pulp-platform/ara/docs/source/images/shuffling_logic_vary_sew.png

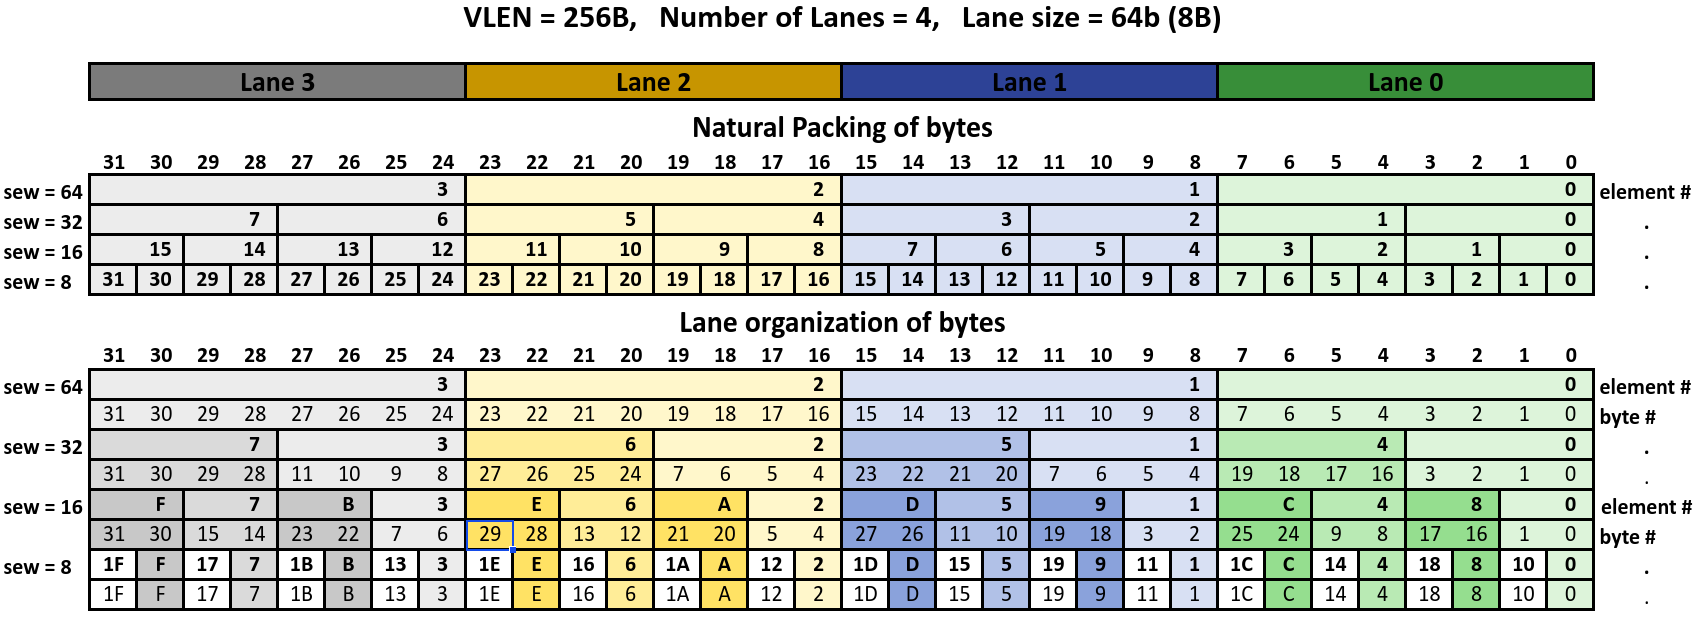
docs/source/images/shuffling_logic_vary_sew.png
