pulp-platform/ara/apps/fdotproduct/main.c

// Copyright 2022 ETH Zurich and University of Bologna.
//
// SPDX-License-Identifier: Apache-2.0
//
// Licensed under the Apache License, Version 2.0 (the "License");
// you may not use this file except in compliance with the License.
// You may obtain a copy of the License at
//
//    http://www.apache.org/licenses/LICENSE-2.0
//
// Unless required by applicable law or agreed to in writing, software
// distributed under the License is distributed on an "AS IS" BASIS,
// WITHOUT WARRANTIES OR CONDITIONS OF ANY KIND, either express or implied.
// See the License for the specific language governing permissions and
// limitations under the License.

// Author: Matteo Perotti <mperotti@iis.ee.ethz.ch>

#include <stdint.h>
#include <string.h>

#include "runtime.h"
#include "util.h"

#include "kernel/fdotproduct.h"

#ifdef SPIKE
#include <stdio.h>
#elif defined ARA_LINUX
#include <stdio.h>
#else
#include "printf.h"
#endif

// Threshold for FP comparisons
#define THRESHOLD_64b 0.0000000001
#define THRESHOLD_32b 0.0001
#define THRESHOLD_16b 1

// Run also the scalar benchmark
#define SCALAR 1

// Check the vector results against golden vectors
#define CHECK 1

// Macro to check similarity between two fp-values, wrt a threshold
#define fp_check(a, b, threshold) ((((a - b) < 0) ? b - a : a - b) < threshold)

// Vector size (Byte)
extern uint64_t vsize;
// Input vectors
extern double v64a[] __attribute__((aligned(32 * NR_LANES), section(".l2")));
extern double v64b[] __attribute__((aligned(32 * NR_LANES), section(".l2")));
extern float v32a[] __attribute__((aligned(32 * NR_LANES), section(".l2")));
extern float v32b[] __attribute__((aligned(32 * NR_LANES), section(".l2")));
extern _Float16 v16a[] __attribute__((aligned(32 * NR_LANES), section(".l2")));
extern _Float16 v16b[] __attribute__((aligned(32 * NR_LANES), section(".l2")));
// Golden outputs
extern double gold64;
extern float gold32;
extern _Float16 gold16;
// Output vectors
extern double res64_v, res64_s;
extern float res32_v, res32_s;
extern _Float16 res16_v, res16_s;

int main() {
  printf("\n");
  printf("===========\n");
  printf("=  FDOTP  =\n");
  printf("===========\n");
  printf("\n");
  printf("\n");

  uint64_t runtime_s, runtime_v;

  for (uint64_t avl = 8; avl <= (vsize >> 3); avl *= 8) {
    printf("Calulating 64b dotp with vectors with length = %lu\n", avl);
    start_timer();
    res64_v = fdotp_v64b(v64a, v64b, avl);
    stop_timer();
    runtime_v = get_timer();
    printf("Vector runtime: %ld\n", runtime_v);

    if (SCALAR) {
      start_timer();
      res64_s = fdotp_s64b(v64a, v64b, avl);
      stop_timer();
      runtime_s = get_timer();
      printf("Scalar runtime: %ld\n", runtime_s);
    }

    if (CHECK) {
      if (SCALAR) {
        printf("Checking results: v = %f, s = %f\n", res64_v, res64_s);
        if (!similarity_check(res64_v, res64_s, THRESHOLD_64b)) {
          printf("Error: v = %f, s = %f\n", res64_v, res64_s);
          return -1;
        }
      }
    }
  }

  for (uint64_t avl = 8; avl <= (vsize >> 2); avl *= 8) {
    printf("Calulating 32b dotp with vectors with length = %lu\n", avl);
    start_timer();
    res32_v = fdotp_v32b(v32a, v32b, avl);
    stop_timer();
    runtime_v = get_timer();
    printf("Vector runtime: %ld\n", runtime_v);

    if (SCALAR) {
      start_timer();
      res32_s = fdotp_s32b(v32a, v32b, avl);
      stop_timer();
      runtime_s = get_timer();
      printf("Scalar runtime: %ld\n", runtime_s);
    }

    if (CHECK) {
      if (SCALAR) {
        printf("Checking results: v = %f, s = %f\n", res32_v, res32_s);
        if (!similarity_check(res32_v, res32_s, THRESHOLD_32b)) {
          printf("Error: v = %f, s = %f\n", res32_v, res32_s);
          return -1;
        }
      }
    }
  }

  for (uint64_t avl = 8; avl <= (vsize >> 2); avl *= 8) {
    // Dotp
    printf("Calulating 16b dotp with vectors with length = %lu\n", avl);
    start_timer();
    res16_v = fdotp_v16b(v16a, v16b, avl);
    stop_timer();
    runtime_v = get_timer();
    printf("Vector runtime: %ld\n", runtime_v);

    if (SCALAR) {
      start_timer();
      res16_s = fdotp_s16b(v16a, v16b, avl);
      stop_timer();
      runtime_s = get_timer();
      printf("Scalar runtime: %ld\n", runtime_s);
    }

    if (CHECK) {
      if (SCALAR) {
        printf("Checking results: v = %x, s = %x\n", *((uint16_t *)&res16_v),
               *((uint16_t *)&res16_s));
        if (!similarity_check(res16_v, res16_s, THRESHOLD_16b)) {
          printf("Error: v = %x, s = %x\n", *((uint16_t *)&res16_v),
                 *((uint16_t *)&res16_s));
          return -1;
        }
      }
    }
  }

  printf("SUCCESS.\n");

  return 0;
}
