pulp-platform/ara/hardware/src/sldu/sldu.sv

// Copyright 2021 ETH Zurich and University of Bologna.
// Solderpad Hardware License, Version 0.51, see LICENSE for details.
// SPDX-License-Identifier: SHL-0.51
//
// Author: Matheus Cavalcante <matheusd@iis.ee.ethz.ch>
// Description:
// This is Ara's slide unit. It is responsible for running the vector slide (up/down)
// instructions, which need access to the whole Vector Register File.

module sldu import ara_pkg::*; import rvv_pkg::*; #(
    parameter  int  unsigned NrLanes        = 0,
    parameter  int  unsigned VLEN           = 0,
    parameter  crypto_support_e CryptoSupport = CryptoSupportNone,
    parameter  type          vaddr_t        = logic, // Type used to address vector register file elements,
    parameter  type          pe_req_t       = logic,
    parameter  type          pe_resp_t      = logic,
    // Dependant parameters. DO NOT CHANGE!
    localparam int  unsigned DataWidth = $bits(elen_t), // Width of the lane datapath
    localparam int  unsigned StrbWidth = DataWidth/8,
    localparam type          strb_t    = logic [StrbWidth-1:0], // Byte-strobe type
    localparam type          vlen_t    = logic[$clog2(VLEN+1)-1:0]
  ) (
    input  logic                   clk_i,
    input  logic                   rst_ni,
    // Interface with the main sequencer
    input  pe_req_t                pe_req_i,
    input  logic                   pe_req_valid_i,
    input  logic     [NrVInsn-1:0] pe_vinsn_running_i,
    output logic                   pe_req_ready_o,
    output pe_resp_t               pe_resp_o,
    // Interface with the lanes
    input  elen_t    [NrLanes-1:0] sldu_operand_i,
    input  logic     [NrLanes-1:0] sldu_operand_valid_i,
    output logic     [NrLanes-1:0] sldu_operand_ready_o,
    output logic     [NrLanes-1:0] sldu_result_req_o,
    output vid_t     [NrLanes-1:0] sldu_result_id_o,
    output vaddr_t   [NrLanes-1:0] sldu_result_addr_o,
    output elen_t    [NrLanes-1:0] sldu_result_wdata_o,
    output strb_t    [NrLanes-1:0] sldu_result_be_o,
    input  logic     [NrLanes-1:0] sldu_result_gnt_i,
    input  logic     [NrLanes-1:0] sldu_result_final_gnt_i,
    // Support for reductions
    output sldu_mux_e              sldu_mux_sel_o,
    output logic     [NrLanes-1:0] sldu_red_valid_o,
    // Interface with the Mask Unit
    input  strb_t    [NrLanes-1:0] mask_i,
    input  logic     [NrLanes-1:0] mask_valid_i,
    output logic                   mask_ready_o
  );

  `include "common_cells/registers.svh"

  import cf_math_pkg::idx_width;

  localparam int unsigned AesColsPerLane  = DataWidth / 32;
  localparam int unsigned AesColsPerGroup = 4;

  ////////////////////////////////
  //  Vector instruction queue  //
  ////////////////////////////////

  // We store a certain number of in-flight vector instructions
  localparam VInsnQueueDepth = SlduInsnQueueDepth;

  struct packed {
    pe_req_t [VInsnQueueDepth-1:0] vinsn;

    // Each instruction can be in one of the three execution phases.
    // - Being accepted (i.e., it is being stored for future execution in this
    //   vector functional unit).
    // - Being issued (i.e., its micro-operations are currently being issued
    //   to the corresponding functional units).
    // - Being committed (i.e., its results are being written to the vector
    //   register file).
    // We need pointers to index which instruction is at each execution phase
    // between the VInsnQueueDepth instructions in memory.
    logic [idx_width(VInsnQueueDepth)-1:0] accept_pnt;
    logic [idx_width(VInsnQueueDepth)-1:0] issue_pnt;
    logic [idx_width(VInsnQueueDepth)-1:0] commit_pnt;

    // We also need to count how many instructions are queueing to be
    // issued/committed, to avoid accepting more instructions than
    // we can handle.
    logic [idx_width(VInsnQueueDepth):0] issue_cnt;
    logic [idx_width(VInsnQueueDepth):0] commit_cnt;
  } vinsn_queue_d, vinsn_queue_q;

  pe_req_t vinsn_issue_q;
  logic vinsn_issue_valid_q;
  // Is the vector instruction queue full?
  logic vinsn_queue_full;
  assign vinsn_queue_full = (vinsn_queue_q.commit_cnt == VInsnQueueDepth);

  // Do we have a vector instruction ready to be issued?
  `FF(vinsn_issue_q, vinsn_queue_d.vinsn[vinsn_queue_d.issue_pnt], '0)
  `FF(vinsn_issue_valid_q, vinsn_queue_d.issue_cnt != '0, 1'b0)

  // Do we have a vector instruction with results being committed?
  pe_req_t vinsn_commit;
  logic    vinsn_commit_valid;
  assign vinsn_commit       = vinsn_queue_q.vinsn[vinsn_queue_q.commit_pnt];
  assign vinsn_commit_valid = (vinsn_queue_q.commit_cnt != '0);

  always_ff @(posedge clk_i or negedge rst_ni) begin
    if (!rst_ni) begin
      vinsn_queue_q <= '0;
    end else begin
      vinsn_queue_q <= vinsn_queue_d;
    end
  end

  /////////////////////
  //  Result queues  //
  /////////////////////

  localparam int unsigned ResultQueueDepth = 2;

  // There is a result queue per lane, holding the results that were not
  // yet accepted by the corresponding lane.
  typedef struct packed {
    vid_t id;
    vaddr_t addr;
    elen_t wdata;
    strb_t be;
  } payload_t;

  // Result queue
  payload_t [ResultQueueDepth-1:0][NrLanes-1:0] result_queue_d, result_queue_q;
  logic     [ResultQueueDepth-1:0][NrLanes-1:0] result_queue_valid_d, result_queue_valid_q;
  // We need two pointers in the result queue. One pointer to
  // indicate with `payload_t` we are currently writing into (write_pnt),
  // and one pointer to indicate which `payload_t` we are currently
  // reading from and writing into the lanes (read_pnt).
  logic     [idx_width(ResultQueueDepth)-1:0]   result_queue_write_pnt_d, result_queue_write_pnt_q;
  logic     [idx_width(ResultQueueDepth)-1:0]   result_queue_read_pnt_d, result_queue_read_pnt_q;
  // We need to count how many valid elements are there in this result queue.
  logic     [idx_width(ResultQueueDepth):0]     result_queue_cnt_d, result_queue_cnt_q;
  // Vector to register the final grants from the operand requesters, which indicate
  // that the result was actually written in the VRF (while the normal grant just says
  // that the result was accepted by the operand requester stage
  logic     [NrLanes-1:0]                       result_final_gnt_d, result_final_gnt_q;

  // Is the result queue full?
  logic result_queue_full;
  assign result_queue_full = (result_queue_cnt_q == ResultQueueDepth);
  // Is the result queue empty?
  logic result_queue_empty;
  assign result_queue_empty = (result_queue_cnt_q == '0);

  always_ff @(posedge clk_i or negedge rst_ni) begin: p_result_queue_ff
    if (!rst_ni) begin
      result_queue_q           <= '0;
      result_queue_valid_q     <= '0;
      result_queue_write_pnt_q <= '0;
      result_queue_read_pnt_q  <= '0;
      result_queue_cnt_q       <= '0;
    end else begin
      result_queue_q           <= result_queue_d;
      result_queue_valid_q     <= result_queue_valid_d;
      result_queue_write_pnt_q <= result_queue_write_pnt_d;
      result_queue_read_pnt_q  <= result_queue_read_pnt_d;
      result_queue_cnt_q       <= result_queue_cnt_d;
    end
  end

  ////////////////////////////////
  //  Spill-reg from the lanes  //
  ////////////////////////////////

  elen_t [NrLanes-1:0] sldu_operand;
  logic  [NrLanes-1:0] sldu_operand_valid;
  logic  [NrLanes-1:0] sldu_operand_ready;

  // Don't handshake if the operands target the addrgen!
  // Moreover, when computing NP2 slides, loop over the same data!
  elen_t [NrLanes-1:0] sldu_operand_d;
  logic [NrLanes-1:0]  sldu_operand_valid_d;
  logic [NrLanes-1:0]  sldu_operand_ready_q;

  typedef enum logic {
    NP2_BUFFER_PNT,
    NP2_RESULT_PNT
  } np2_result_queue_pnt_e;

  typedef enum logic {
    NP2_EXT_SEL,
    NP2_LOOP_SEL
  } np2_loop_mux_e;
  np2_loop_mux_e np2_loop_mux_sel_d, np2_loop_mux_sel_q;

  logic slide_np2_buf_valid_d, slide_np2_buf_valid_q;

  // There are multiple transmitters (TX) (OpQueue, ALU, FPU, SLDU-NP2) and receivers (RX) (SLDU, ADDRGEN).
  // Hypotheses:
  // - When valid is asserted on the RX, data cannot change anymore until the handshake happens.
  // - When valid is received by RX, then DATA is targeting that RX only.
  // Data and handshakes signals are controlled upstream (TX side) so that this Hypotheses hold.

  for (genvar l = 0; l < NrLanes; l++) begin
    spill_register #(
      .T(elen_t)
    ) i_sldu_spill_register (
      .clk_i  (clk_i                      ),
      .rst_ni (rst_ni                     ),
      .valid_i(sldu_operand_valid_d[l]    ),
      .ready_o(sldu_operand_ready_q[l]    ),
      .data_i (sldu_operand_d[l]          ),
      .valid_o(sldu_operand_valid[l]      ),
      .ready_i(sldu_operand_ready[l]      ),
      .data_o (sldu_operand[l]            )
    );

    assign sldu_operand_d[l] = np2_loop_mux_sel_q == NP2_EXT_SEL
                             ? sldu_operand_i[l]
                             : result_queue_q[NP2_BUFFER_PNT][l].wdata;

    assign sldu_operand_valid_d[l] = np2_loop_mux_sel_q == NP2_EXT_SEL
                                   ? sldu_operand_valid_i[l]
                                   : slide_np2_buf_valid_q;

    assign sldu_operand_ready_o[l] = np2_loop_mux_sel_q == NP2_EXT_SEL
                                   ? sldu_operand_ready_q[l]
                                   : 1'b0;
  end

  //////////////////////////
  //  Cut from the masku  //
  //////////////////////////

  strb_t [NrLanes-1:0] mask_q;
  logic  [NrLanes-1:0] mask_valid_d, mask_valid_q;
  logic                mask_ready_d;
  logic  [NrLanes-1:0] mask_ready_q;

  for (genvar l = 0; l < NrLanes; l++) begin
    spill_register #(
      .T(strb_t)
    ) i_mask_operand_register (
      .clk_i     (clk_i           ),
      .rst_ni    (rst_ni          ),
      .data_o    (mask_q[l]       ),
      .valid_o   (mask_valid_q[l] ),
      .ready_i   (mask_ready_d    ),
      .data_i    (mask_i[l]       ),
      .valid_i   (mask_valid_d[l] ),
      .ready_o   (mask_ready_q[l] )
    );

    // Sample only SLDU mask valid
    assign mask_valid_d[l] = mask_valid_i[l] & ~vinsn_issue_q.vm & vinsn_issue_valid_q;
  end


  // Don't upset the masku with a spurious ready
  assign mask_ready_o = mask_ready_q[0] & mask_valid_i[0] & ~vinsn_issue_q.vm & vinsn_issue_valid_q & !(vinsn_issue_q.vfu inside {VFU_Alu, VFU_MFpu});

  ///////////////////
  //  NP2 Support  //
  ///////////////////

  // The SLDU only supports powers of two (p2) strides
  // Decompose the non-power-of-two (np2) slide in multiple p2 slides

  // We implement the np2 support here and fully process every input packet
  // singularly to comply with the undisturbed policy. We cannot use the VRF
  // as intermediate buffer; each VRF write is a commit.

  typedef logic [idx_width(8*NrLanes)-1:0] stride_t;

  stride_t                                  p2_stride_gen_stride_d;
  logic                                     p2_stride_gen_valid_d;
  logic                                     p2_stride_gen_update_d;
  logic [idx_width(idx_width(8*NrLanes)):0] p2_stride_gen_popc_q;
  stride_t                                  p2_stride_gen_stride_q;
  logic                                     p2_stride_gen_valid_q;

  p2_stride_gen #(
    .NrLanes (NrLanes)
  ) i_p2_stride_gen (
    .clk_i       (clk_i                 ),
    .rst_ni      (rst_ni                ),
    .stride_i    (p2_stride_gen_stride_d),
    .valid_i     (p2_stride_gen_valid_d ),
    .update_i    (p2_stride_gen_update_d),
    .popc_o      (p2_stride_gen_popc_q  ),
    .stride_p2_o (p2_stride_gen_stride_q),
    .valid_o     (p2_stride_gen_valid_q )
  );

  //////////////////
  //  Reductions  //
  //////////////////

  // Inter-lane reductions are performed with a logarithmic tree, and the result is
  // accumulated in the last Lane. Then, in the end, the result is passed to the first
  // lane for SIMD reduction
  logic [idx_width(NrLanes)-1:0] red_stride_cnt_d, red_stride_cnt_q;
  logic [idx_width(NrLanes):0] red_stride_cnt_d_wide;

  logic is_issue_reduction, is_issue_alu_reduction, is_issue_vmfpu_reduction;

  assign is_issue_alu_reduction   = vinsn_issue_valid_q & (vinsn_issue_q.vfu == VFU_Alu)
                                  & !(Zvkned(CryptoSupport) && vinsn_issue_q.op inside {[VAESDM_VV:VAESKF2]});
  assign is_issue_vmfpu_reduction = vinsn_issue_valid_q & (vinsn_issue_q.vfu == VFU_MFpu);
  assign is_issue_reduction       = is_issue_alu_reduction | is_issue_vmfpu_reduction;

  // AES ops routed through the SLDU (ShiftRows for round ops, prefix-XOR for key schedule)
  logic is_issue_aes;
  if (Zvkned(CryptoSupport)) begin : gen_aes_issue
    assign is_issue_aes = vinsn_issue_valid_q & (vinsn_issue_q.op inside {[VAESDM_VV:VAESKF2]});
  end else begin : gen_no_aes_issue
    assign is_issue_aes = 1'b0;
  end

  // Active lane mask for AES ops: when VL < 2*NrLanes (less than one full beat),
  // only lanes 0..num_active_cols-1 participate. Column c maps to lane (c % NrLanes).
  // issue_cnt_q is in bytes; each column = 4 bytes.
  logic [NrLanes-1:0] aes_lane_mask;
  always_comb begin
    aes_lane_mask = '1;
    if (is_issue_aes) begin
      for (int unsigned l = 0; l < NrLanes; l++)
        aes_lane_mask[l] = (l < (issue_cnt_q >> 2)) || (issue_cnt_q >= (NrLanes * 8));
    end
  end

  always_comb begin
    sldu_mux_sel_o = NO_RED;
    if (((is_issue_alu_reduction || is_issue_aes) && !(vinsn_commit_valid && vinsn_commit.vfu != VFU_Alu)) || (vinsn_commit_valid && vinsn_commit.vfu == VFU_Alu)) begin
      sldu_mux_sel_o = ALU_RED;
    end else if ((is_issue_vmfpu_reduction && !(vinsn_commit_valid && vinsn_commit.vfu != VFU_MFpu)) || (vinsn_commit_valid && vinsn_commit.vfu == VFU_MFpu)) begin
      sldu_mux_sel_o = MFPU_RED;
    end
  end

  /////////////////////
  //  SLDU DataPath  //
  /////////////////////

  // Input/output non-flat operands
  elen_t [NrLanes-1:0] sld_op_src;
  elen_t [NrLanes-1:0] sld_op_dst;

  // Input and output eew for reshuffling
  rvv_pkg::vew_e sld_eew_src;
  rvv_pkg::vew_e sld_eew_dst;

  // 0: slidedown, 1: slideup
  logic sld_dir;

  // The SLDU slides by powers of two
  logic [idx_width(4*NrLanes):0] sld_slamt;

  sldu_op_dp #(
    .NrLanes  (NrLanes    )
  ) i_sldu_op_dp (
    .op_i     (sld_op_src ),
    .slamt_i  (sld_slamt  ),
    .eew_src_i(sld_eew_src),
    .eew_dst_i(sld_eew_dst),
    .dir_i    (sld_dir    ),
    .op_o     (sld_op_dst )
  );

  //////////////////
  //  Slide unit  //
  //////////////////

  // Vector instructions currently running
  logic [NrVInsn-1:0] vinsn_running_d, vinsn_running_q;

  // Interface with the main sequencer
  pe_resp_t pe_resp;

  // State of the slide FSM
  typedef enum logic [3:0] {
    SLIDE_IDLE,
    SLIDE_RUN,
    SLIDE_RUN_VSLIDE1UP_FIRST_WORD,
    SLIDE_RUN_OSUM,
    SLIDE_WAIT_OSUM,
    SLIDE_NP2_SETUP,
    SLIDE_NP2_RUN,
    SLIDE_NP2_COMMIT,
    SLIDE_NP2_WAIT
  } slide_state_e;
  slide_state_e state_d, state_q;

  logic  [8*NrLanes-1:0] out_en_flat, out_en_seq;
  strb_t [NrLanes-1:0]   out_en;

  // Pointers in the input operand and the output result
  logic   [idx_width(NrLanes*StrbWidth):0] in_pnt_d, in_pnt_q;
  logic   [idx_width(NrLanes*StrbWidth):0] out_pnt_d, out_pnt_q;
  vaddr_t                                  vrf_pnt_d, vrf_pnt_q;

  // Remaining bytes of the current instruction in the issue phase
  vlen_t issue_cnt_d, issue_cnt_q;
  // Respected by default: input_limit_d  = 8*NrLanes + out_pnt_d - in_pnt_d;
  // To enforce: output_limit_d = out_pnt_d + issue_cnt_d;
  // MAXVL == VLEN (when LMUL == 8, i.e., the maximum possible)
  logic [idx_width(VLEN+1):0] output_limit_d, output_limit_q;

  // Remaining bytes of the current instruction in the commit phase
  vlen_t commit_cnt_d, commit_cnt_q;

  /////////////////////////////////////
  //  AES Datapath (SLDU, gated)     //
  /////////////////////////////////////

  elen_t [NrLanes-1:0] aes_shift_result;
  elen_t [NrLanes-1:0] aes_kf1_result;

  if (Zvkned(CryptoSupport)) begin : gen_aes_sldu

    // ShiftRows / InvShiftRows byte permutation across AES columns.
    // With SEW=32, each AES element group is 128 bits = 4x32-bit columns.
    // Each 64-bit lane carries AesColsPerLane columns, so a beat may contain
    // multiple AES groups depending on NrLanes.
    //
    // Column layout within a 32-bit word: [7:0]=row0, [15:8]=row1, [23:16]=row2, [31:24]=row3
    //
    // ShiftRows:    row r shifts LEFT  by r across columns
    // InvShiftRows: row r shifts RIGHT by r across columns

    always_comb begin
      aes_shift_result = '0;

      for (int unsigned l = 0; l < NrLanes; l++) begin
        for (int unsigned half = 0; half < AesColsPerLane; half++) begin
          automatic int unsigned out_col_idx   = half * NrLanes + l;
          automatic int unsigned group_base    = (out_col_idx / AesColsPerGroup) * AesColsPerGroup;
          automatic int unsigned col_in_group  = out_col_idx % AesColsPerGroup;
          automatic int unsigned bit_base      = half * 32;
          automatic int unsigned row1_src_col;
          automatic int unsigned row2_src_col;
          automatic int unsigned row3_src_col;
          automatic int unsigned row1_src_lane;
          automatic int unsigned row2_src_lane;
          automatic int unsigned row3_src_lane;
          automatic int unsigned row1_src_half;
          automatic int unsigned row2_src_half;
          automatic int unsigned row3_src_half;

          if (vinsn_issue_q.op inside {VAESEM_VV, VAESEF_VV, VAESEM_VS, VAESEF_VS}) begin
            row1_src_col = group_base + ((col_in_group + 1) % AesColsPerGroup);
            row2_src_col = group_base + ((col_in_group + 2) % AesColsPerGroup);
            row3_src_col = group_base + ((col_in_group + 3) % AesColsPerGroup);
          end else begin
            row1_src_col = group_base + ((col_in_group + 3) % AesColsPerGroup);
            row2_src_col = group_base + ((col_in_group + 2) % AesColsPerGroup);
            row3_src_col = group_base + ((col_in_group + 1) % AesColsPerGroup);
          end

          row1_src_lane = row1_src_col % NrLanes;
          row2_src_lane = row2_src_col % NrLanes;
          row3_src_lane = row3_src_col % NrLanes;
          row1_src_half = row1_src_col / NrLanes;
          row2_src_half = row2_src_col / NrLanes;
          row3_src_half = row3_src_col / NrLanes;

          aes_shift_result[l][bit_base +  0 +: 8] = sldu_operand[l            ][bit_base              +  0 +: 8];
          aes_shift_result[l][bit_base +  8 +: 8] = sldu_operand[row1_src_lane][row1_src_half * 32 +  8 +: 8];
          aes_shift_result[l][bit_base + 16 +: 8] = sldu_operand[row2_src_lane][row2_src_half * 32 + 16 +: 8];
          aes_shift_result[l][bit_base + 24 +: 8] = sldu_operand[row3_src_lane][row3_src_half * 32 + 24 +: 8];
        end
      end
    end

    // Key schedule prefix-XOR chain (shared by vaeskf1 and vaeskf2).
    // Input from VALU: [w0, w1, w2, temp] where temp = SubWord(RotWord(w3)) ^ Rcon
    // Output to VALU:  [nw0, nw1, nw2, nw2] where nwi = wi ^ nw(i-1), nw(-1) = temp
    // The w3 position gets nw2 so the VALU can compute nw3 = w3 ^ nw2.

    localparam int unsigned AesGroupsPerBeat = (NrLanes * AesColsPerLane) / AesColsPerGroup;

    function automatic logic [31:0] kf1_extract(
      input elen_t [NrLanes-1:0] data,
      input int unsigned col
    );
      kf1_extract = data[col % NrLanes][(col / NrLanes) * 32 +: 32];
    endfunction

    always_comb begin
      aes_kf1_result = '0;

      for (int unsigned grp = 0; grp < AesGroupsPerBeat; grp++) begin
        automatic logic [31:0] w0   = kf1_extract(sldu_operand, grp * 4 + 0);
        automatic logic [31:0] w1   = kf1_extract(sldu_operand, grp * 4 + 1);
        automatic logic [31:0] w2   = kf1_extract(sldu_operand, grp * 4 + 2);
        automatic logic [31:0] temp = kf1_extract(sldu_operand, grp * 4 + 3);

        automatic logic [31:0] nw0 = w0 ^ temp;
        automatic logic [31:0] nw1 = w1 ^ nw0;
        automatic logic [31:0] nw2 = w2 ^ nw1;

        automatic int unsigned c0_lane = (grp * 4 + 0) % NrLanes;
        automatic int unsigned c0_half = (grp * 4 + 0) / NrLanes;
        automatic int unsigned c1_lane = (grp * 4 + 1) % NrLanes;
        automatic int unsigned c1_half = (grp * 4 + 1) / NrLanes;
        automatic int unsigned c2_lane = (grp * 4 + 2) % NrLanes;
        automatic int unsigned c2_half = (grp * 4 + 2) / NrLanes;
        automatic int unsigned c3_lane = (grp * 4 + 3) % NrLanes;
        automatic int unsigned c3_half = (grp * 4 + 3) / NrLanes;

        aes_kf1_result[c0_lane][c0_half * 32 +: 32] = nw0;
        aes_kf1_result[c1_lane][c1_half * 32 +: 32] = nw1;
        aes_kf1_result[c2_lane][c2_half * 32 +: 32] = nw2;
        aes_kf1_result[c3_lane][c3_half * 32 +: 32] = nw2; // w3 position gets nw2
      end
    end

  end else begin : gen_no_aes_sldu
    assign aes_shift_result = '0;
    assign aes_kf1_result   = '0;
  end

  always_comb begin: p_sldu
    // Maintain state
    vinsn_queue_d = vinsn_queue_q;
    issue_cnt_d   = issue_cnt_q;
    commit_cnt_d  = commit_cnt_q;
    in_pnt_d      = in_pnt_q;
    out_pnt_d     = out_pnt_q;
    vrf_pnt_d     = vrf_pnt_q;
    state_d       = state_q;

    result_queue_d           = result_queue_q;
    result_queue_valid_d     = result_queue_valid_q;
    result_queue_read_pnt_d  = result_queue_read_pnt_q;
    result_queue_write_pnt_d = result_queue_write_pnt_q;
    result_queue_cnt_d       = result_queue_cnt_q;

    result_final_gnt_d = result_final_gnt_q;

    // Vector instructions currently running
    vinsn_running_d = vinsn_running_q & pe_vinsn_running_i;

    out_en_flat    = '0;
    out_en_seq     = '0;
    out_en         = '0;
    output_limit_d = output_limit_q;

    // We are not ready, by default
    pe_resp            = '0;
    mask_ready_d       = 1'b0;
    sldu_operand_ready = '0;

    red_stride_cnt_d = red_stride_cnt_q;

    p2_stride_gen_stride_d = '0;
    p2_stride_gen_valid_d  = 1'b0;
    p2_stride_gen_update_d = 1'b0;

    np2_loop_mux_sel_d    = np2_loop_mux_sel_q;
    slide_np2_buf_valid_d = slide_np2_buf_valid_q;

    red_stride_cnt_d_wide = {red_stride_cnt_q, red_stride_cnt_q[idx_width(NrLanes)-1]};

    // Inform the main sequencer if we are idle
    pe_req_ready_o = !vinsn_queue_full;

    // Slide Unit DP
    sld_op_src  = sldu_operand;
    sld_eew_src = (vinsn_issue_q.vfu inside {VFU_Alu, VFU_MFpu})
                ? vinsn_issue_q.vtype.vsew
                : vinsn_issue_q.eew_vs2;
    sld_eew_dst = vinsn_issue_q.vtype.vsew;
    sld_dir     = (vinsn_issue_q.op == VSLIDEUP) || (vinsn_issue_q.vfu inside {VFU_Alu, VFU_MFpu});
    sld_slamt   = (vinsn_issue_q.vfu inside {VFU_Alu, VFU_MFpu})
                ? red_stride_cnt_q
                : stride_t'(vinsn_issue_q.stride >> vinsn_issue_q.vtype.vsew);

    /////////////////
    //  Slide FSM  //
    /////////////////

    unique case (state_q)
      SLIDE_IDLE: begin
        if (vinsn_issue_valid_q) begin
          state_d   = vinsn_issue_q.is_stride_np2 ? SLIDE_NP2_SETUP : SLIDE_RUN;
          vrf_pnt_d = '0;

          unique case (vinsn_issue_q.op)
            VSLIDEUP: begin
              // vslideup starts reading the source operand from its beginning
              in_pnt_d  = '0;
              // vslideup starts writing the destination vector at the slide offset
              out_pnt_d = vinsn_issue_q.stride[idx_width(8*NrLanes)-1:0];

              // Initialize counters
              issue_cnt_d = vinsn_issue_q.vl << int'(vinsn_issue_q.vtype.vsew);

              // Initialize be-enable-generation ancillary signals
              output_limit_d = vinsn_issue_q.use_scalar_op ? out_pnt_d + issue_cnt_d : issue_cnt_d;

              // Trim vector elements which are not touched by the slide unit
              issue_cnt_d -= vinsn_issue_q.stride[$bits(issue_cnt_d)-1:0];

              // Start writing at the middle of the destination vector
              vrf_pnt_d = vinsn_issue_q.stride >> $clog2(8*NrLanes);

              // Go to SLIDE_RUN_VSLIDE1UP_FIRST_WORD if this is a vslide1up instruction
              if (vinsn_issue_q.use_scalar_op)
                state_d = SLIDE_RUN_VSLIDE1UP_FIRST_WORD;
            end
            VSLIDEDOWN: begin
              // vslidedown starts reading the source operand from the slide offset
              in_pnt_d  = vinsn_issue_q.stride[idx_width(8*NrLanes)-1:0];
              // vslidedown starts writing the destination vector at its beginning
              out_pnt_d = '0;

              // Initialize counters
              issue_cnt_d = vinsn_issue_q.vl << int'(vinsn_issue_q.vtype.vsew);

              // Initialize be-enable-generation ancillary signals
              output_limit_d = vinsn_issue_q.use_scalar_op
                             ? issue_cnt_d - (1 << int'(vinsn_issue_q.vtype.vsew))
                             : issue_cnt_d;

              // Trim the last element of vslide1down, which does not come from the VRF
              if (vinsn_issue_q.use_scalar_op)
                issue_cnt_d -= 1 << int'(vinsn_issue_q.vtype.vsew);
            end
            // Ordered sum reductions
            VFREDOSUM, VFWREDOSUM: begin
              // Ordered redsum instructions doesn't need in/out_pnt
              in_pnt_d  = '0;
              out_pnt_d = '0;

              // The total number of transactions is vl - 1, but the last data is sent
              // to lane 0
              issue_cnt_d  = vinsn_issue_q.vl;

              state_d = SLIDE_RUN_OSUM;
            end
            // AES ops: ShiftRows for round ops, prefix-XOR for key schedule.
            // Each beat processes NrLanes*8 bytes; total bytes = VL * 4 (SEW=32).
            // Note: vsew was overridden to EW64 at accept time, so use EW32 explicitly.
            VAESDM_VV, VAESDF_VV, VAESEM_VV, VAESEF_VV, VAESDM_VS, VAESDF_VS, VAESEM_VS, VAESEF_VS, VAESKF1, VAESKF2:  if (Zvkned(CryptoSupport)) begin
              in_pnt_d  = '0;
              out_pnt_d = '0;
              issue_cnt_d = vinsn_issue_q.vl << unsigned'(rvv_pkg::EW32);
            end
            // Unordered reductions
            default: begin
              // Unordered redsum instructions doesn't need in/out_pnt
              in_pnt_d  = '0;
              out_pnt_d = '0;

              // Initialize issue cnt. Pretend to move NrLanes 64-bit elements for (clog2(NrLanes) + 1) times.
              issue_cnt_d  = (NrLanes * ($clog2(NrLanes) + 1)) << EW64;
            end
          endcase
        end
      end

      SLIDE_RUN, SLIDE_RUN_VSLIDE1UP_FIRST_WORD, SLIDE_NP2_COMMIT: begin
        // Are we ready?
        // During a reduction (vinsn_issue_q.vfu == VFU_Alu/VFU_MFPU) don't wait for mask bits
        if ((&(sldu_operand_valid | ~aes_lane_mask) ||
           (((vinsn_issue_q.stride[$bits(vinsn_issue_q.vl)-1:0] >> vinsn_issue_q.vtype.vsew) >= vinsn_issue_q.vl) &&
           (state_q == SLIDE_RUN_VSLIDE1UP_FIRST_WORD))) &&
           !result_queue_full && (vinsn_issue_q.vm || vinsn_issue_q.vfu inside {VFU_Alu, VFU_MFpu} || (|mask_valid_q)))
        begin

          // How many bytes are we copying from the operand to the destination, in this cycle?
          automatic int in_byte_count = NrLanes * 8 - in_pnt_q;
          automatic int out_byte_count = NrLanes * 8 - out_pnt_q;
          automatic int byte_count = in_byte_count < out_byte_count ? in_byte_count : out_byte_count;

          // Build the sequential byte-output-enable
          for (int unsigned b = 0; b < 8*NrLanes; b++)
            if ((b >= out_pnt_q && b < output_limit_q) || vinsn_issue_q.vfu inside {VFU_Alu, VFU_MFpu})
              out_en_seq[b] = 1'b1;

          // Shuffle the output enable
          for (int unsigned b = 0; b < 8*NrLanes; b++)
            out_en_flat[shuffle_index(b, NrLanes, vinsn_issue_q.vtype.vsew)] = out_en_seq[b];

          // Mask the output enable with the mask vector
          out_en = out_en_flat & ({8*NrLanes{vinsn_issue_q.vm | (vinsn_issue_q.vfu inside {VFU_Alu, VFU_MFpu})}} | mask_q);

          // Write in the correct bytes
          for (int lane = 0; lane < NrLanes; lane++)
            for (int b = 0; b < 8; b++)
              if (out_en[lane][b]) begin
                // For AES ops, use transformed data instead of slide datapath
                // (is_issue_aes is constant 1'b0 when CryptoSupport=None)
                if (is_issue_aes && vinsn_issue_q.op inside {VAESKF1, VAESKF2})
                  result_queue_d[result_queue_write_pnt_q][lane].wdata[8*b +: 8] = aes_kf1_result[lane][8*b +: 8];
                else if (is_issue_aes)
                  result_queue_d[result_queue_write_pnt_q][lane].wdata[8*b +: 8] = aes_shift_result[lane][8*b +: 8];
                else
                  result_queue_d[result_queue_write_pnt_q][lane].wdata[8*b +: 8] = sld_op_dst[lane][8*b +: 8];
                result_queue_d[result_queue_write_pnt_q][lane].be[b]           = 1'b1;
              end

          // Initialize id and addr fields of the result queue requests
          for (int lane = 0; lane < NrLanes; lane++) begin
            result_queue_d[result_queue_write_pnt_q][lane].id   = vinsn_issue_q.id;
            result_queue_d[result_queue_write_pnt_q][lane].addr =
              vaddr(vinsn_issue_q.vd, NrLanes, VLEN) + vrf_pnt_q;
          end

          // Bump pointers (reductions always finish in one shot)
          in_pnt_d    = vinsn_issue_q.vfu inside {VFU_Alu, VFU_MFpu} ? NrLanes * 8                  : in_pnt_q  + byte_count;
          out_pnt_d   = vinsn_issue_q.vfu inside {VFU_Alu, VFU_MFpu} ? NrLanes * 8                  : out_pnt_q + byte_count;
          issue_cnt_d = vinsn_issue_q.vfu inside {VFU_Alu, VFU_MFpu} ? issue_cnt_q - (NrLanes * 8)  : issue_cnt_q - byte_count;

          // In Jump to SLIDE_RUN if stride is P2
          if (state_q != SLIDE_NP2_COMMIT)
            state_d = SLIDE_RUN;

          // If this is a vslide1up instruction, copy the scalar operand to the first word
          if (state_q == SLIDE_RUN_VSLIDE1UP_FIRST_WORD)
            unique case (vinsn_issue_q.vtype.vsew)
              EW8: begin
                result_queue_d[result_queue_write_pnt_q][0].wdata[7:0] =
                  vinsn_issue_q.scalar_op[7:0];
                result_queue_d[result_queue_write_pnt_q][0].be[0:0] =
                  vinsn_issue_q.vm || mask_q[0][0];
              end
              EW16: begin
                result_queue_d[result_queue_write_pnt_q][0].wdata[15:0] =
                  vinsn_issue_q.scalar_op[15:0];
                result_queue_d[result_queue_write_pnt_q][0].be[1:0] =
                  {2{vinsn_issue_q.vm || mask_q[0][0]}};
              end
              EW32: begin
                result_queue_d[result_queue_write_pnt_q][0].wdata[31:0] =
                  vinsn_issue_q.scalar_op[31:0];
                result_queue_d[result_queue_write_pnt_q][0].be[3:0] =
                  {4{vinsn_issue_q.vm || mask_q[0][0]}};
              end
              EW64: begin
                result_queue_d[result_queue_write_pnt_q][0].wdata[63:0] =
                  vinsn_issue_q.scalar_op[63:0];
                result_queue_d[result_queue_write_pnt_q][0].be[7:0] =
                  {8{vinsn_issue_q.vm || mask_q[0][0]}};
              end
            endcase

          // Read a full word from the VRF or finished the instruction
          if (in_pnt_d == NrLanes * 8 || issue_cnt_q <= byte_count) begin
            // Reset the pointer and ask for a new operand
            in_pnt_d           = '0;
            sldu_operand_ready = '1;
            // Left-rotate the logarithmic counter. Hacky way to write it, but it's to
            // deal with the 2-lanes design without complaints from Verilator...
            // wide signal to please the tool
            red_stride_cnt_d_wide = {red_stride_cnt_q, red_stride_cnt_q[idx_width(NrLanes)-1]};
            red_stride_cnt_d      = red_stride_cnt_d_wide[idx_width(NrLanes)-1:0];

            // Reset the input data mux
            np2_loop_mux_sel_d = NP2_EXT_SEL;
            if (state_q == SLIDE_NP2_COMMIT) begin
              // Jump to NP2 setup again
              state_d = SLIDE_NP2_SETUP;
            end
          end

          // Filled up a word to the VRF or finished the instruction
          if (out_pnt_d == NrLanes * 8 || issue_cnt_q <= byte_count) begin
            // Reset the pointer
            out_pnt_d = vinsn_issue_q.vfu inside {VFU_Alu, VFU_MFpu} ? {'0, red_stride_cnt_d, 3'b0} : '0;
            // We used all the bits of the mask
            if (vinsn_issue_q.op inside {VSLIDEUP, VSLIDEDOWN})
              mask_ready_d = !vinsn_issue_q.vm;

            // Increment VRF address
            vrf_pnt_d = vrf_pnt_q + 1;

            // Send result to the VRF
            result_queue_cnt_d += 1;
            // For AES with fewer active lanes than NrLanes, only mark active lanes valid.
            // Inactive lanes have no ALU waiting to grant, so marking them valid would deadlock.
            result_queue_valid_d[result_queue_write_pnt_q] = is_issue_aes ? aes_lane_mask : '1;
            result_queue_write_pnt_d                       = result_queue_write_pnt_q + 1;
            if (result_queue_write_pnt_q == ResultQueueDepth-1)
              result_queue_write_pnt_d = '0;

            if (state_q == SLIDE_NP2_COMMIT) state_d = SLIDE_NP2_WAIT;
          end

          // Finished the operation
          if (issue_cnt_q <= byte_count || (vinsn_issue_q.vfu inside {VFU_Alu, VFU_MFpu} && issue_cnt_q <= 8 * NrLanes)) begin
            // Back to idle
            state_d = SLIDE_IDLE;
            // Reset the logarighmic counter
            red_stride_cnt_d = 1;

            // If this is a vslide1down, fill up the last position with the scalar operand
            if (vinsn_issue_q.op == VSLIDEDOWN && vinsn_issue_q.use_scalar_op) begin
              // Copy the scalar operand to the last word
              automatic int out_seq_byte = issue_cnt_q;
              automatic int out_byte = shuffle_index(out_seq_byte, NrLanes, vinsn_issue_q.vtype.vsew);
              automatic int tgt_lane = out_byte[3 +: $clog2(NrLanes)];
              automatic int tgt_lane_offset = out_byte[2:0];

              unique case (vinsn_issue_q.vtype.vsew)
                EW8: begin
                  result_queue_d[result_queue_write_pnt_q][tgt_lane].wdata[8*tgt_lane_offset +: 8]
                    = vinsn_issue_q.scalar_op[7:0];
                  result_queue_d[result_queue_write_pnt_q][tgt_lane].be[tgt_lane_offset +: 1] =
                    vinsn_issue_q.vm || mask_q[tgt_lane][tgt_lane_offset];
                end
                EW16: begin
                  result_queue_d[result_queue_write_pnt_q][tgt_lane].wdata[8*tgt_lane_offset +: 16]
                    = vinsn_issue_q.scalar_op[15:0];
                  result_queue_d[result_queue_write_pnt_q][tgt_lane].be[tgt_lane_offset +: 2] =
                    {2{vinsn_issue_q.vm || mask_q[tgt_lane][tgt_lane_offset]}};
                end
                EW32: begin
                  result_queue_d[result_queue_write_pnt_q][tgt_lane].wdata[8*tgt_lane_offset +: 32]
                    = vinsn_issue_q.scalar_op[31:0];
                  result_queue_d[result_queue_write_pnt_q][tgt_lane].be[tgt_lane_offset +: 4] =
                    {4{vinsn_issue_q.vm || mask_q[tgt_lane][tgt_lane_offset]}};
                end
                EW64: begin
                  result_queue_d[result_queue_write_pnt_q][tgt_lane].wdata[8*tgt_lane_offset +: 64]
                    = vinsn_issue_q.scalar_op[63:0];
                  result_queue_d[result_queue_write_pnt_q][tgt_lane].be[tgt_lane_offset +: 8] =
                    {8{vinsn_issue_q.vm || mask_q[tgt_lane][tgt_lane_offset]}};
                end
              endcase
            end

            // Increment vector instruction queue pointers and counters
            vinsn_queue_d.issue_pnt += 1;
            vinsn_queue_d.issue_cnt -= 1;
          end
        end
        if (state_q == SLIDE_NP2_COMMIT)
          if (slide_np2_buf_valid_q && sldu_operand_ready_q[0])
            // Reset the buffer-valid if the buffer is read, by default
            slide_np2_buf_valid_d = 1'b0;
      end
      SLIDE_RUN_OSUM: begin
        // Short Note: For ordered sum reduction instruction, only one lane has a valid data, and it is sent to the next lane
        // Don't wait for mask bits
        if (!result_queue_full) begin
          for (int lane = 0; lane < NrLanes; lane++) begin
            if (sldu_operand_valid[lane]) begin
              automatic int tgt_lane = (lane == NrLanes - 1) ? 0 : lane + 1;
              // Send result to lane 0
              if (issue_cnt_q == 1) tgt_lane = 0;

              // Acknowledge the received operand
              sldu_operand_ready[lane] = 1'b1;

              // Send result to next lane
              result_queue_d[result_queue_write_pnt_q][tgt_lane].wdata =
                sldu_operand[lane];
              result_queue_d[result_queue_write_pnt_q][tgt_lane].be =
                {8{vinsn_issue_q.vm}} | mask_q[tgt_lane];
              result_queue_valid_d[result_queue_write_pnt_q][tgt_lane] = '1;

              issue_cnt_d = issue_cnt_q - 1;
            end
          end
        end

        // Finish the operation
        if (issue_cnt_d == '0) begin
          state_d      = SLIDE_WAIT_OSUM;
          // Increment vector instruction queue pointers and counters
          vinsn_queue_d.issue_pnt += 1;
          vinsn_queue_d.issue_cnt -= 1;
        end
      end
      SLIDE_WAIT_OSUM: begin
        // Wait one cycle for the last result processing
        commit_cnt_d = 1'b0;
        state_d      = SLIDE_IDLE;
      end
      SLIDE_NP2_SETUP: begin
        // Prepare the write pointer
        result_queue_write_pnt_d = NP2_BUFFER_PNT;
        // Prepare the read pointer
        result_queue_read_pnt_d = NP2_RESULT_PNT;
        // Setup the mux sel as soon as we get the operands
        if (&(sldu_operand_valid_i | sldu_operand_valid))
          np2_loop_mux_sel_d = NP2_LOOP_SEL;
        // Setup the p2-stride generator
        p2_stride_gen_stride_d = stride_t'(vinsn_issue_q.stride >> vinsn_issue_q.vtype.vsew);
        p2_stride_gen_valid_d  = 1'b1;
        // Start processing the first VRF chunk as soon as the result queue is completely empty
        // and the VRF chunk is complete
        if (np2_loop_mux_sel_q == NP2_LOOP_SEL && result_queue_empty) begin
          state_d = SLIDE_NP2_RUN;
        end
      end
      SLIDE_NP2_RUN: begin
        // Reset the buffer-valid if the buffer is read, by default
        if (slide_np2_buf_valid_q && sldu_operand_ready_q[0])
          slide_np2_buf_valid_d = 1'b0;
        // Setup the current p2 stride
        sld_slamt = p2_stride_gen_stride_q;
        // Slide the operands as soon as valid
        if (&sldu_operand_valid) begin
          for (int unsigned l = 0; l < NrLanes; l++)
            result_queue_d[result_queue_write_pnt_q][l].wdata = sld_op_dst[l];
          slide_np2_buf_valid_d = 1'b1;
          // Operands correctly read
          sldu_operand_ready     = '1;
          // Update the p2 stride
          p2_stride_gen_update_d = 1'b1;
          // Commit the final result
          if (p2_stride_gen_popc_q == {'0, 1'b1} && result_queue_empty) begin
            state_d = SLIDE_NP2_COMMIT;
            // Prepare the write pointer
            result_queue_write_pnt_d = NP2_RESULT_PNT;
          end
        end
      end
      SLIDE_NP2_WAIT: begin
        if (result_queue_empty) begin
          result_queue_read_pnt_d  = NP2_RESULT_PNT;
          result_queue_write_pnt_d = NP2_RESULT_PNT;
          state_d = SLIDE_NP2_COMMIT;
        end
      end
      default:;
    endcase

    //////////////////////////////////
    //  Write results into the VRF  //
    //////////////////////////////////

    for (int lane = 0; lane < NrLanes; lane++) begin: result_write
      sldu_result_req_o[lane]   = result_queue_valid_q[result_queue_read_pnt_q][lane] & (~(vinsn_commit.vfu inside {VFU_Alu, VFU_MFpu}));
      sldu_red_valid_o[lane]    = result_queue_valid_q[result_queue_read_pnt_q][lane] & (vinsn_commit.vfu inside {VFU_Alu, VFU_MFpu});
      sldu_result_addr_o[lane]  = result_queue_q[result_queue_read_pnt_q][lane].addr;
      sldu_result_id_o[lane]    = result_queue_q[result_queue_read_pnt_q][lane].id;
      sldu_result_wdata_o[lane] = result_queue_q[result_queue_read_pnt_q][lane].wdata;
      sldu_result_be_o[lane]    = result_queue_q[result_queue_read_pnt_q][lane].be;

      // Update the final gnt vector
      result_final_gnt_d[lane] |= sldu_result_final_gnt_i[lane];

      // Received a grant from the VRF (slide) or from the FUs (reduction).
      // Deactivate the request, but do not bump the pointers for now.
      if (((vinsn_commit.vfu inside {VFU_Alu, VFU_MFpu} && sldu_red_valid_o[lane]) || sldu_result_req_o[lane]) && sldu_result_gnt_i[lane]) begin
        result_queue_valid_d[result_queue_read_pnt_q][lane] = 1'b0;
        result_queue_d[result_queue_read_pnt_q][lane]       = '0;
        // Reset the final gnt vector since we are now waiting for another final gnt
        result_final_gnt_d[lane] = 1'b0;
      end
    end: result_write

    // All lanes accepted the VRF request
    // If this was the last request, wait for all the final grants!
    // If this is a reduction, no need for the final grants
    if (!(|result_queue_valid_d[result_queue_read_pnt_q]) &&
      (vinsn_commit.vfu inside {VFU_Alu, VFU_MFpu} || (&result_final_gnt_d || commit_cnt_q > (NrLanes * 8))))
      // There is something waiting to be written
      if (!result_queue_empty) begin
        if (state_q != SLIDE_NP2_SETUP)
          // Increment the read pointer
          if (result_queue_read_pnt_q == ResultQueueDepth-1)
            result_queue_read_pnt_d = 0;
          else
            result_queue_read_pnt_d = result_queue_read_pnt_q + 1;

        // Decrement the counter of results waiting to be written
        result_queue_cnt_d -= 1;

        // Decrement the counter of remaining vector elements waiting to be written
        commit_cnt_d = commit_cnt_q - NrLanes * 8;
        if (commit_cnt_q < (NrLanes * 8))
          commit_cnt_d = '0;
      end

    // Finished committing the results of a vector instruction
    if (vinsn_commit_valid && commit_cnt_d == '0) begin
      // Mark the vector instruction as being done
      pe_resp.vinsn_done[vinsn_commit.id] = 1'b1;

      // Update the commit counters and pointers
      vinsn_queue_d.commit_cnt -= 1;
      if (vinsn_queue_d.commit_pnt == VInsnQueueDepth-1)
        vinsn_queue_d.commit_pnt = '0;
      else
        vinsn_queue_d.commit_pnt += 1;

      // Update the commit counter for the next instruction
      if (vinsn_queue_d.commit_cnt != '0) begin
        commit_cnt_d = vinsn_queue_q.vinsn[vinsn_queue_d.commit_pnt].op inside {VSLIDEUP, VSLIDEDOWN}
                     ? vinsn_queue_q.vinsn[vinsn_queue_d.commit_pnt].vl << int'(vinsn_queue_q.vinsn[vinsn_queue_d.commit_pnt].vtype.vsew)
                     : (Zvkned(CryptoSupport) && vinsn_queue_q.vinsn[vinsn_queue_d.commit_pnt].op inside {[VAESDM_VV:VAESKF2]})
                     ? vinsn_queue_q.vinsn[vinsn_queue_d.commit_pnt].vl << unsigned'(rvv_pkg::EW32)
                     : (NrLanes * ($clog2(NrLanes) + 1)) << EW64;

        // Trim vector elements which are not written by the slide unit
        if (vinsn_queue_q.vinsn[vinsn_queue_d.commit_pnt].op == VSLIDEUP &&
            !vinsn_queue_q.vinsn[vinsn_queue_d.commit_pnt].use_scalar_op)
          commit_cnt_d -= vinsn_queue_q.vinsn[vinsn_queue_d.commit_pnt].stride[$bits(commit_cnt_d)-1:0];
      end
    end

    //////////////////////////////
    //  Accept new instruction  //
    //////////////////////////////

    if (!vinsn_queue_full && pe_req_valid_i && !vinsn_running_q[pe_req_i.id] &&
      (pe_req_i.vfu == VFU_SlideUnit || pe_req_i.op inside {[VREDSUM:VWREDSUM], [VFREDUSUM:VFWREDOSUM]}
        || (Zvkned(CryptoSupport) && pe_req_i.op inside {[VAESDM_VV:VAESKF2]}))) begin
      vinsn_queue_d.vinsn[vinsn_queue_q.accept_pnt] = pe_req_i;
      vinsn_running_d[pe_req_i.id]                  = 1'b1;

      // Calculate the slide offset inside the vector register
      if (pe_req_i.op inside {VSLIDEUP, VSLIDEDOWN})
        vinsn_queue_d.vinsn[vinsn_queue_q.accept_pnt].stride = pe_req_i.stride <<
          int'(pe_req_i.vtype.vsew);
      // Always move 64-bit packs of data from one lane to the other
      if (pe_req_i.vfu inside {VFU_Alu, VFU_MFpu})
        vinsn_queue_d.vinsn[vinsn_queue_q.accept_pnt].vtype.vsew = EW64;

      if (vinsn_queue_d.commit_cnt == '0) begin
        if (pe_req_i.op inside {VSLIDEUP, VSLIDEDOWN})
          commit_cnt_d = pe_req_i.vl << int'(pe_req_i.vtype.vsew);
        else if (Zvkned(CryptoSupport) && pe_req_i.op inside {[VAESDM_VV:VAESKF2]})
          commit_cnt_d = pe_req_i.vl << int'(pe_req_i.vtype.vsew);
        else
          commit_cnt_d = (NrLanes * ($clog2(NrLanes) + 1)) << EW64;
        // Trim vector elements which are not written by the slide unit
        // VSLIDE1UP always writes at least 1 element
        if (pe_req_i.op == VSLIDEUP && !pe_req_i.use_scalar_op) begin
          commit_cnt_d -= vinsn_queue_d.vinsn[vinsn_queue_q.accept_pnt].stride[$bits(commit_cnt_d)-1:0];
        end
      end

      // Bump pointers and counters of the vector instruction queue
      vinsn_queue_d.accept_pnt += 1;
      vinsn_queue_d.issue_cnt += 1;
      vinsn_queue_d.commit_cnt += 1;
    end
  end: p_sldu

  always_ff @(posedge clk_i or negedge rst_ni) begin
    if (!rst_ni) begin
      vinsn_running_q       <= '0;
      issue_cnt_q           <= '0;
      commit_cnt_q          <= '0;
      in_pnt_q              <= '0;
      out_pnt_q             <= '0;
      vrf_pnt_q             <= '0;
      output_limit_q        <= '0;
      state_q               <= SLIDE_IDLE;
      pe_resp_o             <= '0;
      result_final_gnt_q    <= '0;
      red_stride_cnt_q      <= 1;
      np2_loop_mux_sel_q    <= NP2_EXT_SEL;
      slide_np2_buf_valid_q <= 1'b0;
    end else begin
      vinsn_running_q       <= vinsn_running_d;
      issue_cnt_q           <= issue_cnt_d;
      commit_cnt_q          <= commit_cnt_d;
      in_pnt_q              <= in_pnt_d;
      out_pnt_q             <= out_pnt_d;
      vrf_pnt_q             <= vrf_pnt_d;
      output_limit_q        <= output_limit_d;
      state_q               <= state_d;
      pe_resp_o             <= pe_resp;
      result_final_gnt_q    <= result_final_gnt_d;
      red_stride_cnt_q      <= red_stride_cnt_d;
      np2_loop_mux_sel_q    <= np2_loop_mux_sel_d;
      slide_np2_buf_valid_q <= slide_np2_buf_valid_d;
    end
  end

endmodule: sldu
