pulp-platform/ara/hardware/include/ara_pkg.sv

// Copyright 2021 ETH Zurich and University of Bologna.
// Solderpad Hardware License, Version 0.51, see LICENSE for details.
// SPDX-License-Identifier: SHL-0.51
//
// Author: Matheus Cavalcante <matheusd@iis.ee.ethz.ch>
// Description:
// Ara's main package, containing most of the definitions for its usage.

package ara_pkg;

  //////////////////
  //  Parameters  //
  //////////////////

  // Maximum size of a single vector element, in bits.
  // Ara only supports vector elements up to 64 bits.
  localparam int unsigned ELEN  = 64;
  // Maximum size of a single vector element, in bytes.
  localparam int unsigned ELENB = ELEN / 8;

  // Number of vector instructions that can run in parallel.
  localparam int unsigned NrVInsn = 8;

  // Maximum number of lanes that Ara can support.
  localparam int unsigned MaxNrLanes = 16;

  // Ara Features.

  // Fixed-point support
  typedef enum logic {
    FixedPointDisable = 1'b0,
    FixedPointEnable  = 1'b1
  } fixpt_support_e;

  // Support for segment memory operations
  typedef enum logic {
    SegSupportDisable = 1'b0,
    SegSupportEnable  = 1'b1
  } seg_support_e;

  // FP support outside of the FPU (external)
  // vfrec7, vfrsqrt7, round-toward-odd
  typedef enum logic {
    FPExtSupportDisable = 1'b0,
    FPExtSupportEnable  = 1'b1
  } fpext_support_e;

  // The six bits correspond to {RVVD, RVVF, RVVH, RVVHA, RVVB, RVVBA}
  typedef enum logic [5:0] {
    FPUSupportNone             = 6'b000000,
    FPUSupportHalf             = 6'b001000,
    FPUSupportSingle           = 6'b010000,
    FPUSupportHalfSingle       = 6'b011000,
    FPUSupportDouble           = 6'b100000,
    FPUSupportSingleDouble     = 6'b110000,
    FPUSupportHalfSingleDouble = 6'b111000,
    FPUSupportAll              = 6'b111111
  } fpu_support_e;

  function automatic logic RVVD(fpu_support_e e);
    return e[5];
  endfunction : RVVD

  function automatic logic RVVF(fpu_support_e e);
    return e[4];
  endfunction : RVVF

  function automatic logic RVVH(fpu_support_e e);
    return e[3];
  endfunction : RVVH

  function automatic logic RVVHA(fpu_support_e e);
    return e[2];
  endfunction : RVVHA
  function automatic logic RVVB(fpu_support_e e);
    return e[1];
  endfunction : RVVB
  function automatic logic RVVBA(fpu_support_e e);
    return e[0];
  endfunction : RVVBA

  // 16 bits correspond to {Zvbb, Zvbc, Zvkb, Zvkg, Zvkned, Zvknha, Zvknhb, Zvksed, Zvksh, Zvkn, Zvknc, Zvkng, Zvks, Zvksc, Zvksg, Zvkt}
  typedef enum bit [15:0] {
    CryptoSupportNone          = 16'h0000,
    CryptoSupportBitmanip      = 16'h2000,
    CryptoSupportBasicBit      = 16'hA000,
    CryptoSupportAES           = 16'h0800,
    CryptoSupportBitAES        = 16'h2800,
    CryptoSupportBasicAES      = 16'hA800
  } crypto_support_e;

  function automatic bit Zvbb(crypto_support_e e);
    return e[15];
  endfunction

  function automatic bit Zvkb(crypto_support_e e);
    return e[15] | e[13];
  endfunction

  function automatic bit Zvkned(crypto_support_e e);
    return e[11];
  endfunction

  // Multiplier latencies.
  localparam int unsigned LatMultiplierEW64 = 1;
  localparam int unsigned LatMultiplierEW32 = 1;
  localparam int unsigned LatMultiplierEW16 = 1;
  localparam int unsigned LatMultiplierEW8  = 0;

  // FPU latencies.
  localparam int unsigned LatFCompEW64    = 'd5;
  localparam int unsigned LatFCompEW32    = 'd4;
  localparam int unsigned LatFCompEW16    = 'd3;
  localparam int unsigned LatFCompEW8     = 'd2;
  localparam int unsigned LatFCompEW16Alt = 'd3;
  localparam int unsigned LatFCompEW8Alt  = 'd2;
  localparam int unsigned LatFDivSqrt     = 'd3;
  localparam int unsigned LatFNonComp     = 'd1;
  localparam int unsigned LatFConv        = 'd2;
  localparam int unsigned LatFDotp        = 'd0;
  // Define the maximum FPU latency
  localparam int unsigned LatFMax = LatFCompEW64;

  // Define the maximum instruction queue depth
  localparam MaxVInsnQueueDepth = 4;
  // FUs instruction queue depth.
  localparam int unsigned MfpuInsnQueueDepth = 4;
  localparam int unsigned ValuInsnQueueDepth = 4;
  localparam int unsigned VlduInsnQueueDepth = 4;
  localparam int unsigned VstuInsnQueueDepth = 4;
  localparam int unsigned VaddrgenInsnQueueDepth = 4;
  localparam int unsigned SlduInsnQueueDepth = 2;
  localparam int unsigned NoneInsnQueueDepth = 1;
  // Ara supports MaskuInsnQueueDepth = 1 only.
  localparam int unsigned MaskuInsnQueueDepth = 1;

  ///////////////////
  //  Definitions  //
  ///////////////////

  typedef logic [$clog2(NrVInsn)-1:0] vid_t;
  typedef logic [ELEN-1:0] elen_t;

  //////////////////
  //  Operations  //
  //////////////////

  typedef enum logic [7:0] {
    // Arithmetic and logic instructions
    VADD, VSUB, VADC, VSBC, VRSUB, VMINU, VMIN, VMAXU, VMAX, VAND, VOR, VXOR,
    // Zvbb / Zvkb
    VANDN, VBREV8, VBREV, VCLZ, VCTZ, VCPOPV, VREV8, VROL, VROR, VWSLL,
    // Fixed point
    VSADDU, VSADD, VSSUBU, VSSUB, VAADDU, VAADD, VASUBU, VASUB, VSSRL, VSSRA, VNCLIP, VNCLIPU,
    // Shifts,
    VSLL, VSRL, VSRA, VNSRL, VNSRA,
    // Merge
    VMERGE,
    // Scalar moves to VRF
    VMVSX, VFMVSF,
    // Integer Reductions
    VREDSUM, VREDAND, VREDOR, VREDXOR, VREDMINU, VREDMIN, VREDMAXU, VREDMAX, VWREDSUMU, VWREDSUM,
    // Vector Crypto AES instructions (Zvkned)
    // .vv round ops (need both ALU + SlideUnit for multi-phase execution)
    VAESDM_VV, VAESDF_VV, VAESEM_VV, VAESEF_VV,
    // .vs round ops, key schedule, round zero (ALU only for now)
    VAESDM_VS, VAESDF_VS, VAESEM_VS, VAESEF_VS,
    VAESKF1, VAESKF2, VAESZ_VS,
    // Mul/Mul-Add
    VMUL, VMULH, VMULHU, VMULHSU, VMACC, VNMSAC, VMADD, VNMSUB,
    // Fixed point multiplication
    VSMUL,
    // Div
    VDIVU, VDIV, VREMU, VREM,
    // FPU
    VFADD, VFSUB, VFRSUB, VFMUL, VFDIV, VFRDIV, VFMACC, VFNMACC, VFMSAC, VFNMSAC, VFMADD, VFNMADD, VFMSUB,
    VFNMSUB, VFSQRT, VFMIN, VFMAX, VFREC7, VFRSQRT7, VFCLASS, VFSGNJ, VFSGNJN, VFSGNJX, VFCVTXUF, VFCVTXF, VFCVTFXU, VFCVTFX,
    VFCVTRTZXUF, VFCVTRTZXF, VFNCVTRODFF, VFCVTFF,
    // Floating-point reductions
    VFREDUSUM, VFREDOSUM, VFREDMIN, VFREDMAX, VFWREDUSUM, VFWREDOSUM,
    // Floating-point comparison instructions
    VMFEQ, VMFLE, VMFLT, VMFNE, VMFGT, VMFGE,
    // Integer comparison instructions
    VMSEQ, VMSNE, VMSLTU, VMSLT, VMSLEU, VMSLE, VMSGTU, VMSGT,
    // Integer add-with-carry and subtract-with-borrow carry-out instructions
    VMADC, VMSBC,
    // Mask to mask
    VMSBF, VMSOF, VMSIF,
    // Mask to non-mask
    VIOTA, VID,
    // Mask to scalar
    VCPOP, VFIRST,
    // Mask operations
    VMANDNOT, VMAND, VMOR, VMXOR, VMORNOT, VMNAND, VMNOR, VMXNOR,
    // Complex permutations
    VRGATHER, VRGATHEREI16, VCOMPRESS,
    // Scalar moves from VRF
    VMVXS, VFMVFS,
    // Slide instructions
    VSLIDEUP, VSLIDEDOWN,
    // Load instructions
    VLE, VLSE, VLXE,
    // Store instructions
    VSE, VSSE, VSXE
  } ara_op_e;

  // Return true if op is a load operation
  function automatic logic is_load(ara_op_e op);
    is_load = op inside {[VLE:VLXE]};
  endfunction : is_load

  // Return true if op is a store operation
  function automatic logic is_store(ara_op_e op);
    is_store = op inside {[VSE:VSXE]};
  endfunction : is_store

  // Return true of op is either VCPOP or VFIRST
  function automatic logic vd_scalar(ara_op_e op);
    vd_scalar = op inside {[VCPOP:VFIRST]};
  endfunction : vd_scalar

  typedef enum logic [1:0] {
    NO_RED,
    ALU_RED,
    MFPU_RED
  } sldu_mux_e;

  ////////////////////////
  //  Width conversion  //
  ////////////////////////

  // Some instructions mix vector element widths. For example, widening integers, vwadd.vv,
  // operate on 2*SEW = SEW + SEW. In Ara, we would out the whole instruction on 2*SEW.
  //
  // The operand queues are responsible for taking an element of width EEW and converting it on
  // an element of width SEW for the functional units. The operand queues support the following
  // type conversions:

  localparam int unsigned NumConversions = 10;

  typedef enum logic [$clog2(NumConversions)-1:0] {
    OpQueueConversionNone,
    OpQueueConversionZExt2,
    OpQueueConversionSExt2,
    OpQueueConversionZExt4,
    OpQueueConversionSExt4,
    OpQueueConversionZExt8,
    OpQueueConversionSExt8,
    OpQueueConversionWideFP2,
    OpQueueReductionZExt,
    OpQueueAdjustFPCvt
  } opqueue_conversion_e;
  // OpQueueAdjustFPCvt is introduced to support widening FP conversions, to comply with the
  // required SIMD input format of the FPU module (fpnew)

  // The FPU needs to know if, during the conversion, there is also a width change
  // Moreover, the operand requester treats widening instructions differently for handling WAW
  // CVT_WIDE is equal to 2'b00 since these bits are reused with reductions
  // (this is a hack to save wires)
  // Also for floating-point reduction, it is reused as neutral value
  // 00: zero, 01: positive infinity, 10: negative infinity
  typedef enum logic [1:0] {
    CVT_WIDE   = 2'b00,
    CVT_SAME   = 2'b01,
    CVT_NARROW = 2'b10
  } resize_e;

  // Floating-Point structs for re-encoding during widening FP operations
typedef struct packed {
    logic s;
    logic [3:0] e;
    logic [2:0] m;
  } fp8alt_t;

  typedef struct packed {
    logic s;
    logic [4:0] e;
    logic [1:0] m;
  } fp8_t;

  typedef struct packed {
    logic s;
    logic [7:0] e;
    logic [6:0] m;
  } fp16alt_t;

  typedef struct packed {
    logic s;
    logic [4:0] e;
    logic [9:0] m;
  } fp16_t;

  typedef struct packed {
    logic s;
    logic [7:0] e;
    logic [22:0] m;
  } fp32_t;

  typedef struct packed {
    logic s;
    logic [10:0] e;
    logic [51:0] m;
  } fp64_t;

  function automatic int unsigned fp_mantissa_bits(rvv_pkg::vew_e fp_dtype, logic is_alt);
    unique case ({fp_dtype, is_alt})
      {rvv_pkg::EW8,  1'b0}: fp_mantissa_bits = 2;
      {rvv_pkg::EW8,  1'b1}: fp_mantissa_bits = 3;
      {rvv_pkg::EW16, 1'b0}: fp_mantissa_bits = 10;
      {rvv_pkg::EW16, 1'b1}: fp_mantissa_bits = 7;
      {rvv_pkg::EW32, 1'b0}: fp_mantissa_bits = 23;
      {rvv_pkg::EW64, 1'b0}: fp_mantissa_bits = 52;
      default: fp_mantissa_bits = -1;
    endcase
  endfunction

  function automatic fp16_t fp16_from_fp8(fp8_t fp8, logic [$clog2(fp_mantissa_bits(rvv_pkg::EW8, 0)):0] fp8_m_lzc);
    automatic fp8_t fp8_temp;
    automatic fp16_t fp16;
    // Wide sign
    fp16.s = fp8.s;
    // Wide exponent
    // 15 - 7 = 8
    unique case(fp8.e)
      '0:      fp16.e = (fp8.m == '0) ? '0 : 5'd8 - {3'd0, fp8_m_lzc}; // Zero or Subnormal
      '1:      fp16.e = '1; // NaN
      default: fp16.e = 5'd8 + fp8.e; // Normal
    endcase
    // Wide mantissa
    // If the input is NaN, output a quiet NaN mantissa.
    // Otherwise, append trailing zeros to the mantissa.
    fp8_temp.m = ((fp8.e == '0) && (fp8.m != '0)) ? (fp8.m << 1) << fp8_m_lzc : fp8.m;
    fp16.m = ((fp8.e == '1) && (fp8.m != '0) ) ? {1'b1, 9'b0} : {fp8_temp.m, 8'b0};
    fp16_from_fp8 = fp16;
  endfunction

  function automatic fp32_t fp32_from_fp16(fp16_t fp16, logic [$clog2(fp_mantissa_bits(rvv_pkg::EW16, 0)):0] fp16_m_lzc);
    automatic fp16_t fp16_temp;
    automatic fp32_t fp32;

    // Wide sign
    fp32.s = fp16.s;

    // Wide exponent
    // 127 - 15 = 112
    unique case(fp16.e)
      '0:      fp32.e = (fp16.m == '0) ? '0 : 8'd112 - {4'd0, fp16_m_lzc}; // Zero or Subnormal
      '1:      fp32.e = '1; // NaN
      default: fp32.e = 8'd112 + {3'd0, fp16.e}; // Normal
    endcase

    // Wide mantissa
    // If the input is NaN, output a quiet NaN mantissa.
    // Otherwise, append trailing zeros to the mantissa.
    fp16_temp.m = ((fp16.e == '0) && (fp16.m != '0)) ? (fp16.m << 1) << fp16_m_lzc : fp16.m;
    fp32.m = ((fp16.e == '1) && (fp16.m != '0) ) ? {1'b1, 22'b0} : {fp16_temp.m, 13'b0};

    fp32_from_fp16 = fp32;
  endfunction

  function automatic fp64_t fp64_from_fp32(fp32_t fp32, logic [$clog2(fp_mantissa_bits(rvv_pkg::EW32, 0)):0] fp32_m_lzc);
    automatic fp32_t fp32_temp;
    automatic fp64_t fp64;

    // Wide sign
    fp64.s = fp32.s;

    // Wide exponent
    // 1023 - 127 = 896
    unique case(fp32.e)
      '0:      fp64.e = (fp32.m == '0) ? '0 : 11'd896 - {6'd0, fp32_m_lzc}; // Zero or Subnormal
      '1:      fp64.e = '1; // NaN
      default: fp64.e = 11'd896 + {3'd0, fp32.e}; // Normal
    endcase

    // Wide mantissa
    // If the input is NaN, output a quiet NaN mantissa.
    // Otherwise, append trailing zeros to the mantissa.
    fp32_temp.m = ((fp32.e == '0) && (fp32.m != '0)) ? (fp32.m << 1) << fp32_m_lzc : fp32.m;
    fp64.m = ((fp32.e == '1) && (fp32.m != '0)) ? {1'b1, 51'b0} : {fp32_temp.m, 29'b0};

    fp64_from_fp32 = fp64;
  endfunction

  ////////////////////
  //  PE interface  //
  ////////////////////

  // Those are Ara's VFUs.
  //
  // It is important that all the VFUs that can write back to the VRF
  // are grouped towards the beginning of the enumeration. The store unit
  // cannot do so, therefore it is at the end of the enumeration.
  localparam int unsigned NrVFUs = 7;
  typedef enum logic [$clog2(NrVFUs)-1:0] {
    VFU_Alu, VFU_MFpu, VFU_SlideUnit, VFU_MaskUnit, VFU_LoadUnit, VFU_StoreUnit, VFU_None
  } vfu_e;

  // Internally, each lane is treated as a processing element, between indexes
  // 0 and NrLanes-1. Besides such PEs, functional units that act at a global
  // scale also are with index given by NrLanes plus the following offset.
  //
  // The load and the store unit must be at the beginning of this enumeration.
  typedef enum logic [1:0] {
    OffsetLoad, OffsetStore, OffsetMask, OffsetSlide
  } vfu_offset_e;

  /* The VRF data is stored into the lanes in a shuffled way, similar to how it was done
   * in version 0.9 of the RISC-V Vector Specification, when SLEN < VLEN. In fact, VRF
   * data is organized in lanes as in section 4.3 of the RVV Specification v0.9, with
   * the striping distance set to SLEN = 64, the lane width.
   *
   * As an example, with four lanes, the elements of a vector register are organized
   * as follows.
   *
   * Byte:      1F 1E 1D 1C 1B 1A 19 18 | 17 16 15 14 13 12 11 10 | 0F 0E 0D 0C 0B 0A 09 08 | 07 06 05 04 03 02 01 00 |
   *                                    |                         |                         |                         |
   * SEW = 64:                        3 |                       2 |                       1 |                       0 |
   * SEW = 32:            7           3 |           6           2 |           5           1 |           4           0 |
   * SEW = 16:      F     7     B     3 |     E     6     A     2 |     D     5     9     1 |     C     4     8     0 |
   * SEW = 8:   1F  F 17  7 1B  B 13  3 | 1E  E 16  6 1A  A 12  2 | 1D  D 15  5 19  9 11  1 | 1C  C 14  4 18  8 10  0 |
   *
   * Data coming from/going to the lanes must be reshuffled, in order to be organized
   * in a natural way (i.e., with the bits packed simply from the least-significant
   * to the most-significant). This operation is done by the shuffle (natural packing
   * to the lane's organization) and deshuffle (lane's organization to the natural
   * packing) functions.
   */

  function automatic logic [$clog2(8*MaxNrLanes)-1:0] shuffle_index(logic[15:0] byte_idx, int NrLanes, rvv_pkg::vew_e ew);
    // Generate the shuffling of the table above
    unique case (NrLanes)
      1: unique case (ew)
          rvv_pkg::EW64: begin
            automatic logic [$clog2(8)-1:0] idx [7:0];
            idx[7] = 7; idx[6] = 6; idx[5] = 5; idx[4] = 4;
            idx[3] = 3; idx[2] = 2; idx[1] = 1; idx[0] = 0;
            return idx[byte_idx[2:0]];
          end
          rvv_pkg::EW32: begin
            automatic logic [$clog2(8)-1:0] idx [7:0];
            idx[7] = 7; idx[6] = 6; idx[5] = 5; idx[4] = 4;
            idx[3] = 3; idx[2] = 2; idx[1] = 1; idx[0] = 0;
            return idx[byte_idx[2:0]];
          end
          rvv_pkg::EW16: begin
            automatic logic [$clog2(8)-1:0] idx [7:0];
            idx[7] = 7; idx[6] = 6; idx[5] = 3; idx[4] = 2;
            idx[3] = 5; idx[2] = 4; idx[1] = 1; idx[0] = 0;
            return idx[byte_idx[2:0]];
          end
          rvv_pkg::EW8: begin
            automatic logic [$clog2(8)-1:0] idx [7:0];
            idx[7] = 7; idx[6] = 3; idx[5] = 5; idx[4] = 1;
            idx[3] = 6; idx[2] = 2; idx[1] = 4; idx[0] = 0;
            return idx[byte_idx[2:0]];
          end
          default: begin
            automatic logic [$clog2(8)-1:0] idx [7:0];
            idx[7] = 7; idx[6] = 6; idx[5] = 5; idx[4] = 4;
            idx[3] = 3; idx[2] = 2; idx[1] = 1; idx[0] = 0;
            return idx[byte_idx[2:0]];
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
            return idx[byte_idx[6:0]];
          end
        endcase
      default: $error("Error. Supported number of lanes are 1, 2, 4, 8, 16.");
    endcase

  /*automatic logic [$clog2(ELENB*NrLanes)-1:0] [8*MaxNrLanes-1:0] element_shuffle_index;

   unique case (ew)
   rvv_pkg::EW64:
   for (logic [$clog2(ELENB*NrLanes)-1:0] element = 0; element < NrLanes; element++)
   for (int b = 0; b < 8; b++)
   element_shuffle_index[8*(element >> 0) + b] = 8*element + b;
   rvv_pkg::EW32:
   for (logic [$clog2(ELENB*NrLanes)-1:0] element = 0; element < 2*NrLanes; element++)
   for (int b = 0; b < 4; b++)
   element_shuffle_index[4*((element >> 1) + int'(element[0]) * NrLanes*1) + b] = 4*element + b;
   rvv_pkg::EW16:
   for (logic [$clog2(ELENB*NrLanes)-1:0] element = 0; element < 4*NrLanes; element++)
   for (int b = 0; b < 2; b++)
   element_shuffle_index[2*((element >> 2) + int'(element[1]) * NrLanes*1 + int'(element[0]) * NrLanes*2) + b] = 2*element + b;
   rvv_pkg::EW8:
   for (logic [$clog2(ELENB*NrLanes)-1:0] element = 0; element < 8*NrLanes; element++)
   for (int b = 0; b < 1; b++)
   element_shuffle_index[1*((element >> 3) + int'(element[2]) * NrLanes*1 + int'(element[1]) * NrLanes*2 + int'(element[0]) * NrLanes*4) + b] = 1*element + b;
   default:;
   endcase

   return element_shuffle_index[byte_index];*/
  endfunction : shuffle_index

  function automatic logic [$clog2(8*MaxNrLanes)-1:0] deshuffle_index(logic[15:0] byte_index, int NrLanes, rvv_pkg::vew_e ew);
    // Generate the deshuffling of the table above
    unique case (NrLanes)
      1: begin
        automatic logic [$clog2(8)-1:0] index [7:0];
        for (int b = 0; b < 8; b++)
          index[shuffle_index(b, NrLanes, ew)] = b;
        return index[byte_index[2:0]];
      end
      2: begin
        automatic logic [$clog2(16)-1:0] index [15:0];
        for (int b = 0; b < 16; b++)
          index[shuffle_index(b, NrLanes, ew)] = b;
        return index[byte_index[3:0]];
      end
      4: begin
        automatic logic [$clog2(32)-1:0] index [31:0];
        for (int b = 0; b < 32; b++)
          index[shuffle_index(b, NrLanes, ew)] = b;
        return index[byte_index[4:0]];
      end
      8: begin
        automatic logic [$clog2(64)-1:0] index [63:0];
        for (int b = 0; b < 64; b++)
          index[shuffle_index(b, NrLanes, ew)] = b;
        return index[byte_index[5:0]];
      end
      16: begin
        automatic logic [$clog2(128)-1:0] index [127:0];
        for (int b = 0; b < 128; b++)
          index[shuffle_index(b, NrLanes, ew)] = b;
        return index[byte_index[6:0]];
      end
      default: begin
        automatic logic [$clog2(32)-1:0] index [31:0];
        for (int b = 0; b < 32; b++)
          index[shuffle_index(b, NrLanes, ew)] = b;
        return index[byte_index[4:0]];
      end
    endcase
  endfunction : deshuffle_index

  /////////////////////////
  ////// Fixed-Point //////
  /////////////////////////

  typedef logic        vxsat_e;
  typedef logic [1:0]  vxrm_t;

  typedef union packed {
    logic [0:0][7:0] w64;
    logic [1:0][3:0] w32;
    logic [3:0][1:0] w16;
    logic [7:0][0:0] w8;
  } vxsat_t;

  /////////////////////////
  //  MASKU definitions  //
  /////////////////////////

  // Which FU should process the mask unit request?
  localparam int unsigned NrMaskFUnits = 2;
  typedef enum logic [cf_math_pkg::idx_width(NrMaskFUnits)-1:0]{
    MaskFUAlu, MaskFUMFpu
  } masku_fu_e;

  ////////////////////////
  //  Lane definitions  //
  ////////////////////////

  // There are seven operand queues, serving operands to the different functional units of each lane
  localparam int unsigned NrOperandQueues = 9;
  typedef enum logic [$clog2(NrOperandQueues)-1:0] {
    AluA, AluB, MulFPUA, MulFPUB, MulFPUC, MaskB, MaskM, StA, SlideAddrGenA
  } opqueue_e;

  // Each lane has eight VRF banks
  localparam int unsigned NrVRFBanksPerLane = 8;

  // Find the starting address (in bytes) of a vector register chunk of vid
  function automatic logic [63:0] vaddr(logic [4:0] vid, int NrLanes, int vlen);
    int vlenb = vlen / 8;
    // Each vector register spans multiple words in each bank in each lane
    // The start address is the same in every lane
    // Therefore, within each lane, each vector register chunk starts on a given offset
    vaddr = vid * (vlenb / NrLanes / 8);
    // NOTE: For the extensively tested configuration of Ara keeps:
    //        - (VLEN / NrLanes) to 1024;
    //        - NrVRFBanksPerLane equal to 8.
    //        Given so, each vector register will span 2 words across all the banks and lanes,
    //        therefore, vaddr = vid * 16
  endfunction: vaddr

  // Differenciate between SLDU and ADDRGEN operands from opqueue
  typedef enum logic {
    ALU_SLDU     = 1'b0,
    MFPU_ADDRGEN = 1'b1
  } target_fu_e;

  // Due to the shuffled nature of the vector elements inside one lane, the byte enable
  // signal must be generated differently depending on how many valid elements are there.
  // Considering the lane 0 of the previous example, and vector elements of width 8 bits,
  //
  // Byte:      07 06 05 04 03 02 01 00
  // SEW = 8:   1C  C 14  4 18  8 10  0
  //
  // If there are only three valid vector elements (0, 4, and 8), then the byte enable of
  // that word should be 8'b00010101. The position of the i-th vector element inside one
  // lane is is generated using the same shuffle function as shuffle_index, but considering
  // NrLanes = 1.

  // The following function generates a 8-bit wide byte enable signal, based on how many
  // valid elements are there in that lane word, and the element width.

  function automatic logic [ELEN/8-1:0] be(logic [3:0] cnt, rvv_pkg::vew_e ew);
    unique case (ew)
      rvv_pkg::EW8:
        for (int el = 0; el < 8; el++)
          for (int b = 0; b < 1; b++)
            be[shuffle_index(1*el + b, 1, ew)] = el < cnt;
      rvv_pkg::EW16:
        for (int el = 0; el < 4; el++)
          for (int b = 0; b < 2; b++)
            be[shuffle_index(2*el + b, 1, ew)] = el < cnt;
      rvv_pkg::EW32:
        for (int el = 0; el < 2; el++)
          for (int b = 0; b < 4; b++)
            be[shuffle_index(4*el + b, 1, ew)] = el < cnt;
      rvv_pkg::EW64:
        for (int el = 0; el < 1; el++)
          for (int b = 0; b < 8; b++)
            be[shuffle_index(8*el + b, 1, ew)] = el < cnt;
      default:;
    endcase
  endfunction : be

  /////////////////////////////////////////
  //  Vector Load/Store Unit definition  //
  /////////////////////////////////////////

  // The address generation unit makes requests on the AR/AW buses, while the load and
  // store unit handle the R, W, and B buses. The latter need some information about the
  // original request, namely the fields below.
  typedef struct packed {
    axi_pkg::largest_addr_t addr;
    axi_pkg::size_t size;
    axi_pkg::len_t len;
    logic is_load;
    logic is_exception;
  } addrgen_axi_req_t;

  //////////////////////////
  // VRGATHER / VCOMPRESS //
  //////////////////////////

  // Buffer more elements in MaskB opqueue
  // This should be a power of 2
  localparam VrgatherOpQueueBufDepth = 2;

  // Indices are 16-bit at most because of RISC-V V VLEN limitation at 64Kibit
  typedef logic [$clog2(rvv_pkg::RISCV_MAX_VLEN)-1:0] max_vlen_t;

  // During VRGATHER/VCOMPRESS, the MASKU asks for operands to the lanes
  typedef struct packed {
    max_vlen_t idx;
    rvv_pkg::vew_e eew;
    logic [4:0] vs;
    logic is_last_req;
  } vrgat_req_t;

  ////////////////////////
  // VFREC7 & VFRSQRT7 //
  ///////////////////////

  localparam int unsigned LUT_BITS = 7;

  localparam int unsigned E16_BITS = 16;
  localparam int unsigned E32_BITS = 32;
  localparam int unsigned E64_BITS = 64;

  localparam int unsigned EXP_BITS_E16 = 5;
  localparam int unsigned EXP_BITS_E32 = 8;
  localparam int unsigned EXP_BITS_E64 = 11;

  localparam int unsigned VF_TYPE_SEL_BITS = 10;

  localparam logic [4:0]  E16_2xB = 5'd30;
  localparam logic [7:0]  E32_2xB = 8'd254;
  localparam logic [10:0] E64_2xB = 11'd2046;

  localparam logic [15:0] E16_NaN  = 16'h7e00;
  localparam logic [15:0] E16_pInf = 16'h7c00;
  localparam logic [15:0] E16_mInf = 16'hfc00;

  localparam logic [14:0] E16_Max  = 15'h7bff;     // Max Number without sign
  localparam logic [14:0] E16_Inf  = 15'h7c00;     // Inf without sign

  localparam logic [31:0] E32_NaN  = 32'h7fc00000;
  localparam logic [31:0] E32_pInf = 32'h7f800000;
  localparam logic [31:0] E32_mInf = 32'hff800000;

  localparam logic [30:0] E32_Max  = 31'h7f7fffff;  // Max Number without sign
  localparam logic [30:0] E32_Inf  = 31'h7f800000;  // Inf without sign

  localparam logic [63:0] E64_NaN  = 64'h7ff8000000000000;
  localparam logic [63:0] E64_pInf = 64'h7ff0000000000000;
  localparam logic [63:0] E64_mInf = 64'hfff0000000000000;

  localparam logic  [5:0] E16_3xB = 6'd45;
  localparam logic  [8:0] E32_3xB = 9'd381;
  localparam logic [11:0] E64_3xB = 12'd3069;

  localparam logic [62:0] E64_Max  = 63'h7fefffffffffffff; // Max Number without sign
  localparam logic [62:0] E64_Inf  = 63'h7ff0000000000000; // Inf without sign

  // Structure containing 5 bit flag and desired output
 typedef struct packed {
  fpnew_pkg::status_t ex_flag;
  fp16_t              vf7_e16;
 } vf7_flag_out_e16;

  typedef struct packed {
  fpnew_pkg::status_t ex_flag;
  fp32_t              vf7_e32;
  } vf7_flag_out_e32;

 typedef struct packed {
  fpnew_pkg::status_t ex_flag;
  fp64_t              vf7_e64;
  } vf7_flag_out_e64;

  // vfrec7 LUT
  function automatic logic [LUT_BITS-1:0] vfrec7_lut(logic [LUT_BITS-1:0] vfrec7_lut_select);
    logic [LUT_BITS-1:0] vfrec7_lut_out;
    unique case (vfrec7_lut_select)
      7'd0  : vfrec7_lut_out=7'd127;
      7'd1  : vfrec7_lut_out=7'd125;
      7'd2  : vfrec7_lut_out=7'd123;
      7'd3  : vfrec7_lut_out=7'd121;
      7'd4  : vfrec7_lut_out=7'd119;
      7'd5  : vfrec7_lut_out=7'd117;
      7'd6  : vfrec7_lut_out=7'd116;
      7'd7  : vfrec7_lut_out=7'd114;
      7'd8  : vfrec7_lut_out=7'd112;
      7'd9  : vfrec7_lut_out=7'd110;
      7'd10 : vfrec7_lut_out=7'd109;
      7'd11 : vfrec7_lut_out=7'd107;
      7'd12 : vfrec7_lut_out=7'd105;
      7'd13 : vfrec7_lut_out=7'd104;
      7'd14 : vfrec7_lut_out=7'd102;
      7'd15 : vfrec7_lut_out=7'd100;
      7'd16 : vfrec7_lut_out=7'd99;
      7'd17 : vfrec7_lut_out=7'd97;
      7'd18 : vfrec7_lut_out=7'd96;
      7'd19 : vfrec7_lut_out=7'd94;
      7'd20 : vfrec7_lut_out=7'd93;
      7'd21 : vfrec7_lut_out=7'd91;
      7'd22 : vfrec7_lut_out=7'd90;
      7'd23 : vfrec7_lut_out=7'd88;
      7'd24 : vfrec7_lut_out=7'd87;
      7'd25 : vfrec7_lut_out=7'd85;
      7'd26 : vfrec7_lut_out=7'd84;
      7'd27 : vfrec7_lut_out=7'd83;
      7'd28 : vfrec7_lut_out=7'd81;
      7'd29 : vfrec7_lut_out=7'd80;
      7'd30 : vfrec7_lut_out=7'd79;
      7'd31 : vfrec7_lut_out=7'd77;
      7'd32 : vfrec7_lut_out=7'd76;
      7'd33 : vfrec7_lut_out=7'd75;
      7'd34 : vfrec7_lut_out=7'd74;
      7'd35 : vfrec7_lut_out=7'd72;
      7'd36 : vfrec7_lut_out=7'd71;
      7'd37 : vfrec7_lut_out=7'd70;
      7'd38 : vfrec7_lut_out=7'd69;
      7'd39 : vfrec7_lut_out=7'd68;
      7'd40 : vfrec7_lut_out=7'd66;
      7'd41 : vfrec7_lut_out=7'd65;
      7'd42 : vfrec7_lut_out=7'd64;
      7'd43 : vfrec7_lut_out=7'd63;
      7'd44 : vfrec7_lut_out=7'd62;
      7'd45 : vfrec7_lut_out=7'd61;
      7'd46 : vfrec7_lut_out=7'd60;
      7'd47 : vfrec7_lut_out=7'd59;
      7'd48 : vfrec7_lut_out=7'd58;
      7'd49 : vfrec7_lut_out=7'd57;
      7'd50 : vfrec7_lut_out=7'd56;
      7'd51 : vfrec7_lut_out=7'd55;
      7'd52 : vfrec7_lut_out=7'd54;
      7'd53 : vfrec7_lut_out=7'd53;
      7'd54 : vfrec7_lut_out=7'd52;
      7'd55 : vfrec7_lut_out=7'd51;
      7'd56 : vfrec7_lut_out=7'd50;
      7'd57 : vfrec7_lut_out=7'd49;
      7'd58 : vfrec7_lut_out=7'd48;
      7'd59 : vfrec7_lut_out=7'd47;
      7'd60 : vfrec7_lut_out=7'd46;
      7'd61 : vfrec7_lut_out=7'd45;
      7'd62 : vfrec7_lut_out=7'd44;
      7'd63 : vfrec7_lut_out=7'd43;
      7'd64 : vfrec7_lut_out=7'd42;
      7'd65 : vfrec7_lut_out=7'd41;
      7'd66 : vfrec7_lut_out=7'd40;
      7'd67 : vfrec7_lut_out=7'd40;
      7'd68 : vfrec7_lut_out=7'd39;
      7'd69 : vfrec7_lut_out=7'd38;
      7'd70 : vfrec7_lut_out=7'd37;
      7'd71 : vfrec7_lut_out=7'd36;
      7'd72 : vfrec7_lut_out=7'd35;
      7'd73 : vfrec7_lut_out=7'd35;
      7'd74 : vfrec7_lut_out=7'd34;
      7'd75 : vfrec7_lut_out=7'd33;
      7'd76 : vfrec7_lut_out=7'd32;
      7'd77 : vfrec7_lut_out=7'd31;
      7'd78 : vfrec7_lut_out=7'd31;
      7'd79 : vfrec7_lut_out=7'd30;
      7'd80 : vfrec7_lut_out=7'd29;
      7'd81 : vfrec7_lut_out=7'd28;
      7'd82 : vfrec7_lut_out=7'd28;
      7'd83 : vfrec7_lut_out=7'd27;
      7'd84 : vfrec7_lut_out=7'd26;
      7'd85 : vfrec7_lut_out=7'd25;
      7'd86 : vfrec7_lut_out=7'd25;
      7'd87 : vfrec7_lut_out=7'd24;
      7'd88 : vfrec7_lut_out=7'd23;
      7'd89 : vfrec7_lut_out=7'd23;
      7'd90 : vfrec7_lut_out=7'd22;
      7'd91 : vfrec7_lut_out=7'd21;
      7'd92 : vfrec7_lut_out=7'd21;
      7'd93 : vfrec7_lut_out=7'd20;
      7'd94 : vfrec7_lut_out=7'd19;
      7'd95 : vfrec7_lut_out=7'd19;
      7'd96 : vfrec7_lut_out=7'd18;
      7'd97 : vfrec7_lut_out=7'd17;
      7'd98 : vfrec7_lut_out=7'd17;
      7'd99 : vfrec7_lut_out=7'd16;
      7'd100: vfrec7_lut_out=7'd15;
      7'd101: vfrec7_lut_out=7'd15;
      7'd102: vfrec7_lut_out=7'd14;
      7'd103: vfrec7_lut_out=7'd14;
      7'd104: vfrec7_lut_out=7'd13;
      7'd105: vfrec7_lut_out=7'd12;
      7'd106: vfrec7_lut_out=7'd12;
      7'd107: vfrec7_lut_out=7'd11;
      7'd108: vfrec7_lut_out=7'd11;
      7'd109: vfrec7_lut_out=7'd10;
      7'd110: vfrec7_lut_out=7'd9;
      7'd111: vfrec7_lut_out=7'd9;
      7'd112: vfrec7_lut_out=7'd8;
      7'd113: vfrec7_lut_out=7'd8;
      7'd114: vfrec7_lut_out=7'd7;
      7'd115: vfrec7_lut_out=7'd7;
      7'd116: vfrec7_lut_out=7'd6;
      7'd117: vfrec7_lut_out=7'd5;
      7'd118: vfrec7_lut_out=7'd5;
      7'd119: vfrec7_lut_out=7'd4;
      7'd120: vfrec7_lut_out=7'd4;
      7'd121: vfrec7_lut_out=7'd3;
      7'd122: vfrec7_lut_out=7'd3;
      7'd123: vfrec7_lut_out=7'd2;
      7'd124: vfrec7_lut_out=7'd2;
      7'd125: vfrec7_lut_out=7'd1;
      7'd126: vfrec7_lut_out=7'd1;
      7'd127: vfrec7_lut_out=7'd0;
      default: vfrec7_lut_out=7'd0;
    endcase
    return vfrec7_lut_out;
  endfunction : vfrec7_lut

  // vfrec7 result (sew: 16 bit)
  function automatic vf7_flag_out_e16 vfrec7_fp16(logic [VF_TYPE_SEL_BITS-1:0] vfpu_result, logic [E16_BITS-1:0] operand_a_delay, fpnew_pkg::roundmode_e fp_rm_process);
    vf7_flag_out_e16 vfrec7_o, vfrec7_out;

    fp16_t vfrec7_i, vfrec7_n_excep, vfrec7_sub;

    logic select_vfrec7_out;

    logic en_rm;

    vfrec7_o       = 21'd0;
    vfrec7_out     = 21'd0;
    vfrec7_i       = 16'd0;
    vfrec7_n_excep = 16'd0;
    vfrec7_sub     = 16'd0;

    en_rm =  fp_rm_process==fpnew_pkg::RTZ
          ||(fp_rm_process==fpnew_pkg::RDN && ~operand_a_delay[E16_BITS-1])
          ||(fp_rm_process==fpnew_pkg::RUP &&  operand_a_delay[E16_BITS-1]);

      //subnormal inputs with sig=0.. or sig=1..
    unique case (operand_a_delay[9])
      1'b0: begin
        vfrec7_sub.e = 5'd0 - 5'd1;                    //0 minus number of leading zeros in sig
        vfrec7_sub.m = {operand_a_delay[7:0], 2'b00};  //left-shifting by 2
      end
      1'b1: begin
        vfrec7_sub.e = 5'd0;                          //0 minus number of leading zeros in sig
        vfrec7_sub.m = {operand_a_delay[8:0], 1'b0};  //left-shifting by 1
      end
      default:;
    endcase

    unique case (vfpu_result)
      fpnew_pkg::POSSUBNORM,
      fpnew_pkg::NEGSUBNORM: begin //SUBNORMAL
        vfrec7_i.e  = vfrec7_sub.e;
        vfrec7_i.m  = vfrec7_sub.m;
      end
      fpnew_pkg::POSNORM,
      fpnew_pkg::NEGNORM: begin // NORMAL
        vfrec7_i.e  = operand_a_delay[14:10];
        vfrec7_i.m  = operand_a_delay[9:0];
      end
      default: begin
        vfrec7_i.e = 'x;
        vfrec7_i.m = 'x;
      end
    endcase

    unique case (vfpu_result)
      fpnew_pkg::NEGINF: vfrec7_o.vf7_e16 = {1'b1, 15'd0};
      fpnew_pkg::POSINF: vfrec7_o.vf7_e16 = 16'd0;
      fpnew_pkg::SNAN : begin
        vfrec7_o.vf7_e16    = E16_NaN;
        vfrec7_o.ex_flag.NV = 1'b1;
      end
      fpnew_pkg::QNAN : vfrec7_o.vf7_e16 = E16_NaN;
      fpnew_pkg::NEGZERO: begin
        vfrec7_o.vf7_e16    = E16_mInf;
        vfrec7_o.ex_flag.DZ = 1'b1;
      end
      fpnew_pkg::POSZERO: begin
        vfrec7_o.vf7_e16    = E16_pInf;
        vfrec7_o.ex_flag.DZ = 1'b1;
      end
      fpnew_pkg::POSSUBNORM,
      fpnew_pkg::NEGSUBNORM,
      fpnew_pkg::POSNORM,
      fpnew_pkg::NEGNORM: begin
        //Output exponent can be found by
        //exp_o = 2*B-1-exp_i
        //      = 2*B+(~exp_i)
        vfrec7_n_excep.e = E16_2xB +(~vfrec7_i.e);
        //Output significand(mantissa) can be found by using lookup table
        vfrec7_n_excep.m[9:3] = vfrec7_lut(vfrec7_i.m[9:3]);

         //if output is subnormal
         // output exponent is equal to zero
        unique case (vfrec7_n_excep.e)
          5'b0_0000: begin
            vfrec7_o.vf7_e16.e      = 5'b0_0000;
            vfrec7_o.vf7_e16.m[9:2] = {1'b1, vfrec7_n_excep.m[9:3]}; //concating 1 at MSB
          end
          5'b1_1111: begin
            vfrec7_o.vf7_e16.e      = 5'b0_0000;
            vfrec7_o.vf7_e16.m[9:1] = {2'b01, vfrec7_n_excep.m[9:3]}; //concating 1 at MSB and shiting by 1
          end
          default: begin
            vfrec7_o.vf7_e16.e      = vfrec7_n_excep.e;
            vfrec7_o.vf7_e16.m[9:3] = vfrec7_n_excep.m[9:3];
          end
        endcase

         //The output sign equals the input sign.
        vfrec7_o.vf7_e16.s = operand_a_delay[15];
      end
      default:;
    endcase

    // check if input number is subnormal number  with sig=00..
    select_vfrec7_out =  (operand_a_delay[9:8]==2'b00)
                      && (vfpu_result==fpnew_pkg::POSSUBNORM
                      ||  vfpu_result==fpnew_pkg::NEGSUBNORM);

    unique case (select_vfrec7_out)
      1'b0: vfrec7_out = vfrec7_o;
      1'b1:  begin

        // if input number  is subnormal with sig=00.. then
        // output is equal to infinity or  +-finite value (greatest magnitude)
        // depending on rounding modes
        unique case (en_rm)
          1'b0: vfrec7_out.vf7_e16 = {vfrec7_o.vf7_e16.s, E16_Inf}; // infinity
          1'b1: vfrec7_out.vf7_e16 = {vfrec7_o.vf7_e16.s, E16_Max}; // greatest magnitude
          default:;
        endcase

        vfrec7_out.ex_flag.NX  = 1'b1;
        vfrec7_out.ex_flag.OF  = 1'b1;
      end
      default:;
    endcase
    return vfrec7_out;
  endfunction : vfrec7_fp16

  // vfrec7 result (sew: 32 bit)
  function automatic vf7_flag_out_e32 vfrec7_fp32(logic [VF_TYPE_SEL_BITS-1:0] vfpu_result, logic [E32_BITS-1:0] operand_a_delay, fpnew_pkg::roundmode_e fp_rm_process);
    vf7_flag_out_e32 vfrec7_o, vfrec7_out;

    fp32_t vfrec7_i, vfrec7_n_excep, vfrec7_sub;

    logic select_vfrec7_out;
    logic en_rm;

    vfrec7_o       = 37'd0;
    vfrec7_out     = 37'd0;
    vfrec7_i       = 32'd0;
    vfrec7_n_excep = 32'd0;
    vfrec7_sub     = 32'd0;

    en_rm =  fp_rm_process==fpnew_pkg::RTZ
         || (fp_rm_process==fpnew_pkg::RDN && ~operand_a_delay[E32_BITS-1])
         || (fp_rm_process==fpnew_pkg::RUP &&  operand_a_delay[E32_BITS-1]);

    //subnormal inputs with sig=0.. or sig=1..
    unique case (operand_a_delay[22])
      1'b0: begin
        vfrec7_sub.e = 8'd0-8'd1;                    //0 minus number of leading zeros in sig
        vfrec7_sub.m = {operand_a_delay[20:0], 2'b00}; //left-shifting by 2
      end
      1'b1: begin
        vfrec7_sub.e = 8'd0;                          //0 minus number of leading zeros in sig
        vfrec7_sub.m = {operand_a_delay[21:0], 1'b0};  //left-shifting by 1
      end
      default:;
    endcase

    unique case (vfpu_result)
      fpnew_pkg::POSSUBNORM,
      fpnew_pkg::NEGSUBNORM: begin //SUBNORMAL
        vfrec7_i.e  = vfrec7_sub.e;
        vfrec7_i.m  = vfrec7_sub.m;
      end
      fpnew_pkg:: POSNORM,
      fpnew_pkg:: NEGNORM: begin // NORMAL
        vfrec7_i.e  = operand_a_delay[30:23];
        vfrec7_i.m  = operand_a_delay[22:0];
      end
      default: begin
        vfrec7_i.e = 'x;
        vfrec7_i.m = 'x;
      end
    endcase

    unique case (vfpu_result)
      fpnew_pkg::NEGINF: vfrec7_o.vf7_e32 = {1'b1, 31'd0};
      fpnew_pkg::POSINF: vfrec7_o.vf7_e32 = 32'd0;
      fpnew_pkg::SNAN: begin
        vfrec7_o.vf7_e32    = E32_NaN;
        vfrec7_o.ex_flag.NV = 1'b1;
      end
      fpnew_pkg::QNAN: vfrec7_o.vf7_e32 = E32_NaN;
      fpnew_pkg::NEGZERO: begin
        vfrec7_o.vf7_e32    = E32_mInf;
        vfrec7_o.ex_flag.DZ = 1'b1;
      end
      fpnew_pkg::POSZERO: begin
        vfrec7_o.vf7_e32    = E32_pInf;
        vfrec7_o.ex_flag.DZ = 1'b1;
      end
      fpnew_pkg::POSSUBNORM,
      fpnew_pkg::NEGSUBNORM,
      fpnew_pkg::POSNORM,
      fpnew_pkg::NEGNORM: begin
        //Output exponent can be found by
        //exp_o = 2*B-1-exp_i
        //      = 2*B+(~exp_i)
        vfrec7_n_excep.e = E32_2xB +(~vfrec7_i.e);

        //Output significand(mantissa) can be found by using lookup table
        vfrec7_n_excep.m[22:16] = vfrec7_lut(vfrec7_i.m[22:16]);

        //if output is subnormal
        // output exponent is equal to zero
        unique case (vfrec7_n_excep.e)
          8'h00 : begin
            vfrec7_o.vf7_e32.e        = 8'h00;
            vfrec7_o.vf7_e32.m[22:15] = {1'b1, vfrec7_n_excep.m[22:16]}; //concating 1 at MSB
          end
          8'hff : begin
            vfrec7_o.vf7_e32.e        = 8'h00;
            vfrec7_o.vf7_e32.m[22:14] = {2'b01, vfrec7_n_excep.m[22:16]}; //concating 1 at MSB and shiting by 1
          end
          default:  begin
            vfrec7_o.vf7_e32.e        = vfrec7_n_excep.e;
            vfrec7_o.vf7_e32.m[22:15] = vfrec7_n_excep.m[22:15];
          end
        endcase

        //The output sign equals the input sign.
        vfrec7_o.vf7_e32.s = operand_a_delay[31];
      end
      default:;
    endcase

    // check if input number is subnormal number  with sig=00..
    select_vfrec7_out = (operand_a_delay[22:21]==2'b00)
                     && (vfpu_result==fpnew_pkg::POSSUBNORM
                     ||  vfpu_result==fpnew_pkg::NEGSUBNORM);

    unique case (select_vfrec7_out)
      1'b0: vfrec7_out = vfrec7_o;
      1'b1: begin
        // if input number  is subnormal with sig=00.. then
        // output is equal to infinity or  +-finite value (greatest magnitude)
        // depending on rounding modes
        unique case (en_rm)
          1'b0: vfrec7_out.vf7_e32 = {vfrec7_o.vf7_e32.s, E32_Inf}; // infinity
          1'b1: vfrec7_out.vf7_e32 = {vfrec7_o.vf7_e32.s, E32_Max}; // greatest magnitude
          default:;
        endcase

        vfrec7_out.ex_flag.NX  = 1'b1;
        vfrec7_out.ex_flag.OF  = 1'b1;
      end
      default:;
    endcase
    return vfrec7_out;
  endfunction : vfrec7_fp32

  // vfrec7 result (sew: 64 bit)
  function automatic vf7_flag_out_e64 vfrec7_fp64(logic [VF_TYPE_SEL_BITS-1:0] vfpu_result, logic [E64_BITS-1:0] operand_a_delay,fpnew_pkg::roundmode_e fp_rm_process);
    vf7_flag_out_e64 vfrec7_o, vfrec7_out;

    fp64_t vfrec7_i, vfrec7_n_excep, vfrec7_sub;

    logic select_vfrec7_out;
    logic en_rm;

    vfrec7_o       = 69'd0;
    vfrec7_out     = 69'd0;
    vfrec7_i       = 64'd0;
    vfrec7_n_excep = 64'd0;
    vfrec7_sub     = 64'd0;

    en_rm =  fp_rm_process==fpnew_pkg::RTZ
         || (fp_rm_process==fpnew_pkg::RDN && ~operand_a_delay[E64_BITS-1])
         || (fp_rm_process==fpnew_pkg::RUP &&  operand_a_delay[E64_BITS-1]);

    //subnormal inputs with sig=0.. or sig=1..
    unique case (operand_a_delay[51])
      1'b0: begin
        vfrec7_sub.e = 11'd0-11'd1;                    //0 minus number of leading zeros in sig
        vfrec7_sub.m = {operand_a_delay[49:0], 2'b00}; //left-shifting by 2
      end
      1'b1: begin
        vfrec7_sub.e = 11'd0;                          //0 minus number of leading zeros in sig
        vfrec7_sub.m = {operand_a_delay[50:0], 1'b0};  //left-shifting by 1
      end
      default:;
    endcase

    unique case (vfpu_result)
      fpnew_pkg::POSSUBNORM,
      fpnew_pkg::NEGSUBNORM: begin //SUBNORMAL
        vfrec7_i.e  = vfrec7_sub.e;
        vfrec7_i.m  = vfrec7_sub.m;
      end
      fpnew_pkg::POSNORM,
      fpnew_pkg::NEGNORM: begin // NORMAL
        vfrec7_i.e  = operand_a_delay[62:52];
        vfrec7_i.m  = operand_a_delay[51:0];
      end
      default: begin
        vfrec7_i.e = 'x;
        vfrec7_i.m = 'x;
      end
    endcase

    unique case (vfpu_result)
      fpnew_pkg::NEGINF: vfrec7_o.vf7_e64 = {1'b1, 63'd0};
      fpnew_pkg::POSINF: vfrec7_o.vf7_e64 = 64'd0;
      fpnew_pkg::SNAN: begin
        vfrec7_o.vf7_e64    = E64_NaN;
        vfrec7_o.ex_flag.NV = 1'b1;
      end
      fpnew_pkg::QNAN : vfrec7_o.vf7_e64 = E64_NaN;
      fpnew_pkg::NEGZERO: begin
        vfrec7_o.vf7_e64    = E64_mInf;
        vfrec7_o.ex_flag.DZ = 1'b1;
      end
      fpnew_pkg:: POSZERO: begin
        vfrec7_o.vf7_e64    = E64_pInf;
        vfrec7_o.ex_flag.DZ = 1'b1;
      end
      fpnew_pkg::POSSUBNORM,
      fpnew_pkg::NEGSUBNORM,
      fpnew_pkg::POSNORM,
      fpnew_pkg::NEGNORM: begin
        //Output exponent can be found by
        //exp_o = 2*B-1-exp_i
        //      = 2*B+(~exp_i)
        vfrec7_n_excep.e = E64_2xB +(~vfrec7_i.e);

        //Output significand(mantissa) can be found by using lookup table
        vfrec7_n_excep.m[51:45] = vfrec7_lut(vfrec7_i.m[51:45]);

          //if output is subnormal
          // output exponent is equal to zero
        unique case (vfrec7_n_excep.e)
          11'h000 : begin
            vfrec7_o.vf7_e64.e        = 11'h000;
            vfrec7_o.vf7_e64.m[51:44] = {1'b1, vfrec7_n_excep.m[51:45]}; //concating 1 at MSB
          end
          11'h7ff: begin
            vfrec7_o.vf7_e64.e        = 11'h000;
            vfrec7_o.vf7_e64.m[51:43] = {2'b01, vfrec7_n_excep.m[51:45]}; //concating 1 at MSB and shiting by 1
          end
          default:begin
            vfrec7_o.vf7_e64.e        = vfrec7_n_excep.e;
            vfrec7_o.vf7_e64.m[51:45] = vfrec7_n_excep.m[51:45];
          end
        endcase

        //The output sign equals the input sign.
        vfrec7_o.vf7_e64.s = operand_a_delay[63];
      end
      default:;
    endcase

    // check if input number is subnormal number  with sig=00..
    select_vfrec7_out = (operand_a_delay[51:50]==2'b00)
                     && (vfpu_result==fpnew_pkg::POSSUBNORM
                     ||  vfpu_result==fpnew_pkg::NEGSUBNORM);

    unique case (select_vfrec7_out)
      1'b0: vfrec7_out = vfrec7_o;
      1'b1: begin
        // if input number  is subnormal with sig=00.. then
        // output is equal to infinity or  +-finite value (greatest magnitude)
        // depending on rounding modes
        unique case (en_rm)
          1'b0:vfrec7_out.vf7_e64 = {vfrec7_o.vf7_e64.s, E64_Inf}; // infinity
          1'b1:vfrec7_out.vf7_e64 = {vfrec7_o.vf7_e64.s, E64_Max}; // greatest magnitude
          default:;
        endcase

        vfrec7_out.ex_flag.NX  = 1'b1;
        vfrec7_out.ex_flag.OF  = 1'b1;
      end
      default:;
    endcase
    return vfrec7_out;
  endfunction : vfrec7_fp64

  // vfrsqrt7 LUT
  function automatic logic [LUT_BITS-1:0] vfrsqrt7_lut(logic [LUT_BITS-1:0] vfrsqrt7_lut_select);
    logic [LUT_BITS-1:0] vfrsqrt7_lut_out;
    unique case (vfrsqrt7_lut_select)
      7'd0  : vfrsqrt7_lut_out=7'd52;
      7'd1  : vfrsqrt7_lut_out=7'd51;
      7'd2  : vfrsqrt7_lut_out=7'd50;
      7'd3  : vfrsqrt7_lut_out=7'd48;
      7'd4  : vfrsqrt7_lut_out=7'd47;
      7'd5  : vfrsqrt7_lut_out=7'd46;
      7'd6  : vfrsqrt7_lut_out=7'd44;
      7'd7  : vfrsqrt7_lut_out=7'd43;
      7'd8  : vfrsqrt7_lut_out=7'd42;
      7'd9  : vfrsqrt7_lut_out=7'd41;
      7'd10 : vfrsqrt7_lut_out=7'd40;
      7'd11 : vfrsqrt7_lut_out=7'd39;
      7'd12 : vfrsqrt7_lut_out=7'd38;
      7'd13 : vfrsqrt7_lut_out=7'd36;
      7'd14 : vfrsqrt7_lut_out=7'd35;
      7'd15 : vfrsqrt7_lut_out=7'd34;
      7'd16 : vfrsqrt7_lut_out=7'd33;
      7'd17 : vfrsqrt7_lut_out=7'd32;
      7'd18 : vfrsqrt7_lut_out=7'd31;
      7'd19 : vfrsqrt7_lut_out=7'd30;
      7'd20 : vfrsqrt7_lut_out=7'd30;
      7'd21 : vfrsqrt7_lut_out=7'd29;
      7'd22 : vfrsqrt7_lut_out=7'd28;
      7'd23 : vfrsqrt7_lut_out=7'd27;
      7'd24 : vfrsqrt7_lut_out=7'd26;
      7'd25 : vfrsqrt7_lut_out=7'd25;
      7'd26 : vfrsqrt7_lut_out=7'd24;
      7'd27 : vfrsqrt7_lut_out=7'd23;
      7'd28 : vfrsqrt7_lut_out=7'd23;
      7'd29 : vfrsqrt7_lut_out=7'd22;
      7'd30 : vfrsqrt7_lut_out=7'd21;
      7'd31 : vfrsqrt7_lut_out=7'd20;
      7'd32 : vfrsqrt7_lut_out=7'd19;
      7'd33 : vfrsqrt7_lut_out=7'd19;
      7'd34 : vfrsqrt7_lut_out=7'd18;
      7'd35 : vfrsqrt7_lut_out=7'd17;
      7'd36 : vfrsqrt7_lut_out=7'd16;
      7'd37 : vfrsqrt7_lut_out=7'd16;
      7'd38 : vfrsqrt7_lut_out=7'd15;
      7'd39 : vfrsqrt7_lut_out=7'd14;
      7'd40 : vfrsqrt7_lut_out=7'd14;
      7'd41 : vfrsqrt7_lut_out=7'd13;
      7'd42 : vfrsqrt7_lut_out=7'd12;
      7'd43 : vfrsqrt7_lut_out=7'd12;
      7'd44 : vfrsqrt7_lut_out=7'd11;
      7'd45 : vfrsqrt7_lut_out=7'd10;
      7'd46 : vfrsqrt7_lut_out=7'd10;
      7'd47 : vfrsqrt7_lut_out=7'd9;
      7'd48 : vfrsqrt7_lut_out=7'd9;
      7'd49 : vfrsqrt7_lut_out=7'd8;
      7'd50 : vfrsqrt7_lut_out=7'd7;
      7'd51 : vfrsqrt7_lut_out=7'd7;
      7'd52 : vfrsqrt7_lut_out=7'd6;
      7'd53 : vfrsqrt7_lut_out=7'd6;
      7'd54 : vfrsqrt7_lut_out=7'd5;
      7'd55 : vfrsqrt7_lut_out=7'd4;
      7'd56 : vfrsqrt7_lut_out=7'd4;
      7'd57 : vfrsqrt7_lut_out=7'd3;
      7'd58 : vfrsqrt7_lut_out=7'd3;
      7'd59 : vfrsqrt7_lut_out=7'd2;
      7'd60 : vfrsqrt7_lut_out=7'd2;
      7'd61 : vfrsqrt7_lut_out=7'd1;
      7'd62 : vfrsqrt7_lut_out=7'd1;
      7'd63 : vfrsqrt7_lut_out=7'd0;
      7'd64 : vfrsqrt7_lut_out=7'd127;
      7'd65 : vfrsqrt7_lut_out=7'd125;
      7'd66 : vfrsqrt7_lut_out=7'd123;
      7'd67 : vfrsqrt7_lut_out=7'd121;
      7'd68 : vfrsqrt7_lut_out=7'd119;
      7'd69 : vfrsqrt7_lut_out=7'd118;
      7'd70 : vfrsqrt7_lut_out=7'd116;
      7'd71 : vfrsqrt7_lut_out=7'd114;
      7'd72 : vfrsqrt7_lut_out=7'd113;
      7'd73 : vfrsqrt7_lut_out=7'd111;
      7'd74 : vfrsqrt7_lut_out=7'd109;
      7'd75 : vfrsqrt7_lut_out=7'd108;
      7'd76 : vfrsqrt7_lut_out=7'd106;
      7'd77 : vfrsqrt7_lut_out=7'd105;
      7'd78 : vfrsqrt7_lut_out=7'd103;
      7'd79 : vfrsqrt7_lut_out=7'd102;
      7'd80 : vfrsqrt7_lut_out=7'd100;
      7'd81 : vfrsqrt7_lut_out=7'd99;
      7'd82 : vfrsqrt7_lut_out=7'd97;
      7'd83 : vfrsqrt7_lut_out=7'd96;
      7'd84 : vfrsqrt7_lut_out=7'd95;
      7'd85 : vfrsqrt7_lut_out=7'd93;
      7'd86 : vfrsqrt7_lut_out=7'd92;
      7'd87 : vfrsqrt7_lut_out=7'd91;
      7'd88 : vfrsqrt7_lut_out=7'd90;
      7'd89 : vfrsqrt7_lut_out=7'd88;
      7'd90 : vfrsqrt7_lut_out=7'd87;
      7'd91 : vfrsqrt7_lut_out=7'd86;
      7'd92 : vfrsqrt7_lut_out=7'd85;
      7'd93 : vfrsqrt7_lut_out=7'd84;
      7'd94 : vfrsqrt7_lut_out=7'd83;
      7'd95 : vfrsqrt7_lut_out=7'd82;
      7'd96 : vfrsqrt7_lut_out=7'd80;
      7'd97 : vfrsqrt7_lut_out=7'd79;
      7'd98 : vfrsqrt7_lut_out=7'd78;
      7'd99 : vfrsqrt7_lut_out=7'd77;
      7'd100: vfrsqrt7_lut_out=7'd76;
      7'd101: vfrsqrt7_lut_out=7'd75;
      7'd102: vfrsqrt7_lut_out=7'd74;
      7'd103: vfrsqrt7_lut_out=7'd73;
      7'd104: vfrsqrt7_lut_out=7'd72;
      7'd105: vfrsqrt7_lut_out=7'd71;
      7'd106: vfrsqrt7_lut_out=7'd70;
      7'd107: vfrsqrt7_lut_out=7'd70;
      7'd108: vfrsqrt7_lut_out=7'd69;
      7'd109: vfrsqrt7_lut_out=7'd68;
      7'd110: vfrsqrt7_lut_out=7'd67;
      7'd111: vfrsqrt7_lut_out=7'd66;
      7'd112: vfrsqrt7_lut_out=7'd65;
      7'd113: vfrsqrt7_lut_out=7'd64;
      7'd114: vfrsqrt7_lut_out=7'd63;
      7'd115: vfrsqrt7_lut_out=7'd63;
      7'd116: vfrsqrt7_lut_out=7'd62;
      7'd117: vfrsqrt7_lut_out=7'd61;
      7'd118: vfrsqrt7_lut_out=7'd60;
      7'd119: vfrsqrt7_lut_out=7'd59;
      7'd120: vfrsqrt7_lut_out=7'd59;
      7'd121: vfrsqrt7_lut_out=7'd58;
      7'd122: vfrsqrt7_lut_out=7'd57;
      7'd123: vfrsqrt7_lut_out=7'd56;
      7'd124: vfrsqrt7_lut_out=7'd56;
      7'd125: vfrsqrt7_lut_out=7'd55;
      7'd126: vfrsqrt7_lut_out=7'd54;
      7'd127: vfrsqrt7_lut_out=7'd53;
      default: vfrsqrt7_lut_out=7'd53;
    endcase
    return vfrsqrt7_lut_out;
  endfunction : vfrsqrt7_lut

  // vfrsqrt7 results

  // vfrsqrt7 result (sew: 16 bit)
  function automatic vf7_flag_out_e16 vfrsqrt7_fp16(logic [VF_TYPE_SEL_BITS-1:0] vfpu_result, logic [E16_BITS-1:0] operand_a_delay, logic [3:0] leading_zeros_count);
    vf7_flag_out_e16 vfrsqrt7_o;
    fp16_t           vfrsqrt7_i;

    logic [EXP_BITS_E16:0] vfrsqrt7_exp_i, vfrsqrt7_exp_o;

    vfrsqrt7_o     = 21'd0;
    vfrsqrt7_i     = 16'd0;
    vfrsqrt7_exp_o = 6'd0;
    vfrsqrt7_exp_i = 6'd0;

    unique case (vfpu_result[6:5])
      // POSSUBNORM
      2'b01: begin
        // As input is subnormal, So
        // input exponent:
        // 0 minus the number of leading zeros
        vfrsqrt7_exp_i = 6'd0 - ({2'b00, leading_zeros_count});
        // the normalized input significand(mantissa)
        // is given by shifting the input significand left by
        // 1 minus the input exponent
        vfrsqrt7_i.m = operand_a_delay[9:0] << (6'd1 - vfrsqrt7_exp_i);
      end
      // POSNORM
      2'b10: begin
        vfrsqrt7_exp_i = {1'b0, operand_a_delay[14:10]};
        vfrsqrt7_i.m   = operand_a_delay[9:0];
      end
      default: begin
        vfrsqrt7_exp_i = 'x;
        vfrsqrt7_i.m   = 'x;
      end
    endcase

    unique case (vfpu_result)
      fpnew_pkg::NEGINF,
      fpnew_pkg::NEGNORM,
      fpnew_pkg::NEGSUBNORM,
      fpnew_pkg::SNAN: begin
        vfrsqrt7_o.vf7_e16    = E16_NaN;
        vfrsqrt7_o.ex_flag.NV = 1'b1;
      end
      fpnew_pkg::QNAN: vfrsqrt7_o.vf7_e16 = E16_NaN;
      fpnew_pkg::NEGZERO: begin
        vfrsqrt7_o.vf7_e16    = E16_mInf;
        vfrsqrt7_o.ex_flag.DZ = 1'b1;
      end
      fpnew_pkg::POSZERO: begin
        vfrsqrt7_o.vf7_e16    = E16_pInf;
        vfrsqrt7_o.ex_flag.DZ = 1'b1;
      end
      fpnew_pkg::POSINF: vfrsqrt7_o.vf7_e16 = 16'd0;
      fpnew_pkg::POSSUBNORM,
      fpnew_pkg::POSNORM: begin
        // Output exponent can be found by
        // exp_o = (3*B-1-exp_i )/2
        //       = (3*B+(~exp_i))/2
        vfrsqrt7_exp_o = E16_3xB + (~vfrsqrt7_exp_i);
        // Dividing by 2
        vfrsqrt7_o.vf7_e16.e = vfrsqrt7_exp_o[5:1];
        // Output significand(mantissa) can be found by using lookup table
        // The address for LUT is found by concatenating LSB of the normalized input exponent and
        // the six MSBs of the normalized input significand
        vfrsqrt7_o.vf7_e16.m[9:3] = vfrsqrt7_lut({vfrsqrt7_exp_i[0],vfrsqrt7_i.m[9:4]});
        // The output sign equals the input sign.
        vfrsqrt7_o.vf7_e16.s = vfrsqrt7_i.s;
      end
      default:;
    endcase
    return vfrsqrt7_o;
  endfunction : vfrsqrt7_fp16

  // vfrsqrt7 result (sew: 32 bit)
  function automatic vf7_flag_out_e32 vfrsqrt7_fp32(logic [VF_TYPE_SEL_BITS-1:0] vfpu_result, logic [E32_BITS-1:0] operand_a_delay, logic [4:0] leading_zeros_count);
    vf7_flag_out_e32 vfrsqrt7_o;
    fp32_t          vfrsqrt7_i;

    logic [EXP_BITS_E32:0] vfrsqrt7_exp_i, vfrsqrt7_exp_o;

    vfrsqrt7_o     = 37'd0;
    vfrsqrt7_i     = 32'd0;
    vfrsqrt7_exp_o = 9'd0;
    vfrsqrt7_exp_i = 9'd0;

    unique case (vfpu_result[6:5])
      // POSSUBNORM
      2'b01: begin
        //As input is subnormal, So
        //input exponent:
        //0 minus the number of leading zeros
        vfrsqrt7_exp_i = 9'd0 - ({4'b0000, leading_zeros_count});
        //the normalized input significand(mantissa)
        //is given by shifting the input significand left by
        //1 minus the input exponent
        vfrsqrt7_i.m = operand_a_delay[22:0] << (9'd1 - vfrsqrt7_exp_i);
      end
      // POSNORM
      2'b10: begin
        vfrsqrt7_exp_i = {1'b0, operand_a_delay[30:23]};
        vfrsqrt7_i.m   = operand_a_delay[22:0];
      end
      default: begin
        vfrsqrt7_exp_i = 'x;
        vfrsqrt7_i.m   = 'x;
      end
    endcase

    unique case (vfpu_result)
      fpnew_pkg::NEGINF,
      fpnew_pkg::NEGNORM,
      fpnew_pkg::NEGSUBNORM,
      fpnew_pkg::SNAN: begin
        vfrsqrt7_o.vf7_e32    = E32_NaN;
        vfrsqrt7_o.ex_flag.NV = 1'b1;
      end
      fpnew_pkg::QNAN: vfrsqrt7_o.vf7_e32 = E32_NaN;
      fpnew_pkg::NEGZERO: begin
        vfrsqrt7_o.vf7_e32    = E32_mInf;
        vfrsqrt7_o.ex_flag.DZ = 1'b1;
      end
      fpnew_pkg::POSZERO: begin
        vfrsqrt7_o.vf7_e32    = E32_pInf;
        vfrsqrt7_o.ex_flag.DZ = 1'b1;
      end
      fpnew_pkg::POSINF: vfrsqrt7_o.vf7_e32 = 32'd0;
      fpnew_pkg::POSSUBNORM,
      fpnew_pkg::POSNORM: begin
        // Output exponent can be found by
        // exp_o = (3*B-1-exp_i )/2
        //       = (3*B+(~exp_i))/2
        vfrsqrt7_exp_o = E32_3xB + (~vfrsqrt7_exp_i);
        // dividing by 2
        vfrsqrt7_o.vf7_e32.e = vfrsqrt7_exp_o[8:1];
        // Output significand(mantissa) can be found by using lookup table
        // The address for LUT is found by concatenating LSB of the normalized input exponent and
        // the six MSBs of the normalized input significand
        vfrsqrt7_o.vf7_e32.m[22:16] = vfrsqrt7_lut({vfrsqrt7_exp_i[0], vfrsqrt7_i.m[22:17]});
        // The output sign equals the input sign.
        vfrsqrt7_o.vf7_e32.s = vfrsqrt7_i.s;
      end
      default:;
    endcase
    return vfrsqrt7_o;
  endfunction : vfrsqrt7_fp32

  // vfrsqrt7 result (sew: 64 bit)
  function automatic vf7_flag_out_e64 vfrsqrt7_fp64(logic [VF_TYPE_SEL_BITS-1:0] vfpu_result, logic [E64_BITS-1:0] operand_a_delay, logic [5:0] leading_zeros_count);
    vf7_flag_out_e64 vfrsqrt7_o;
    fp64_t           vfrsqrt7_i;

    logic [EXP_BITS_E64:0] vfrsqrt7_exp_i, vfrsqrt7_exp_o;

    vfrsqrt7_o     = 69'd0;
    vfrsqrt7_i     = 64'd0;
    vfrsqrt7_exp_o = 12'd0;
    vfrsqrt7_exp_i = 12'd0;

    unique case (vfpu_result[6:5])
    // POSSUBNORM
    2'b01: begin
      // As input is subnormal, So
      // input exponent:
      // 0 minus the number of leading zeros
      vfrsqrt7_exp_i = 12'd0 - ({6'd0, leading_zeros_count});
      // the normalized input significand(mantissa)
      // is given by shifting the input significand left by
      // 1 minus the input exponent
      vfrsqrt7_i.m = operand_a_delay[51:0] << (12'd1 - vfrsqrt7_exp_i);
    end
    // POSNORM
    2'b10: begin
      vfrsqrt7_exp_i = {1'b0, operand_a_delay[62:52]};
      vfrsqrt7_i.m   = operand_a_delay[51:0];
    end
    default: begin
      vfrsqrt7_exp_i = 'x;
      vfrsqrt7_i.m   = 'x;
    end
    endcase
    unique case (vfpu_result)
       fpnew_pkg::NEGINF,
       fpnew_pkg::NEGNORM,
       fpnew_pkg::NEGSUBNORM,
       fpnew_pkg::SNAN: begin
         vfrsqrt7_o.vf7_e64    = E64_NaN;
         vfrsqrt7_o.ex_flag.NV = 1'b1;
       end
       fpnew_pkg::QNAN: vfrsqrt7_o.vf7_e64 = E64_NaN;
       fpnew_pkg::NEGZERO: begin
         vfrsqrt7_o.vf7_e64    = E64_mInf;
         vfrsqrt7_o.ex_flag.DZ = 1'b1;
       end
       fpnew_pkg::POSZERO: begin
         vfrsqrt7_o.vf7_e64    = E64_pInf;
         vfrsqrt7_o.ex_flag.DZ = 1'b1;
       end
       fpnew_pkg::POSINF: vfrsqrt7_o.vf7_e64 = 64'd0;
       fpnew_pkg::POSSUBNORM,
       fpnew_pkg::POSNORM: begin
         // Output exponent can be found by
         // exp_o = (3*B-1-exp_i )/2
         //       = (3*B+(~exp_i))/2
         vfrsqrt7_exp_o = E64_3xB +(~vfrsqrt7_exp_i);
         // dividing by 2
         vfrsqrt7_o.vf7_e64.e = vfrsqrt7_exp_o[11:1];
         // Output significand(mantissa) can be found by using lookup table
         // The address for LUT is found by concatenating LSB of the normalized input exponent and
         // the six MSBs of the normalized input significand
         vfrsqrt7_o.vf7_e64.m[51:45] = vfrsqrt7_lut({vfrsqrt7_exp_i [0],vfrsqrt7_i.m[51:46]});
         // The output sign equals the input sign.
         vfrsqrt7_o.vf7_e64.s = vfrsqrt7_i.s;
      end
      default:;
    endcase
    return vfrsqrt7_o;
  endfunction : vfrsqrt7_fp64

  ////////////////
  // Exceptions //
  ////////////////

  // End-to-end store exception latency, i.e.,
  // the latency from the addrgen store exception to the opqueues.
  // We keep it as a define to implement conditional declaration.
  `define StuExLat 1
  localparam int unsigned StuExLat = `StuExLat;

endpackage : ara_pkg
