pulp-platform/ara/hardware/src/ara.sv

// Copyright 2021 ETH Zurich and University of Bologna.
// Solderpad Hardware License, Version 0.51, see LICENSE for details.
// SPDX-License-Identifier: SHL-0.51
//
// Author: Matheus Cavalcante <matheusd@iis.ee.ethz.ch>
// Description:
// Ara's top-level, interfacing with Ariane.

module ara import ara_pkg::*; #(
    // RVV Parameters
    parameter  int           unsigned NrLanes      = 0,                          // Number of parallel vector lanes.
    parameter  int           unsigned VLEN         = 0,                          // VLEN [bit]
    parameter  int           unsigned OSSupport    = 1,
    // Support for floating-point data types
    parameter  fpu_support_e          FPUSupport   = FPUSupportHalfSingleDouble,
    // External support for vfrec7, vfrsqrt7
    parameter  fpext_support_e        FPExtSupport = FPExtSupportEnable,
    // Support for fixed-point data types
    parameter  fixpt_support_e        FixPtSupport = FixedPointEnable,
    // Support for segment memory operations
    parameter  seg_support_e          SegSupport   = SegSupportEnable,
    // Support for crypto extension
    parameter  crypto_support_e       CryptoSupport = CryptoSupportNone,
    // CVA6 configuration
    parameter  config_pkg::cva6_cfg_t CVA6Cfg      = cva6_config_pkg::cva6_cfg,
    // CVA6-related parameters
    parameter type                    exception_t        = logic,
    parameter type                    accelerator_req_t  = logic,
    parameter type                    accelerator_resp_t = logic,
    parameter type                    acc_mmu_req_t      = logic,
    parameter type                    acc_mmu_resp_t     = logic,
    parameter type                    cva6_to_acc_t      = logic,
    parameter type                    acc_to_cva6_t      = logic,
    // AXI Interface
    parameter  int           unsigned AxiDataWidth = 0,
    parameter  int           unsigned AxiAddrWidth = 0,
    parameter  type                   axi_ar_t     = logic,
    parameter  type                   axi_r_t      = logic,
    parameter  type                   axi_aw_t     = logic,
    parameter  type                   axi_w_t      = logic,
    parameter  type                   axi_b_t      = logic,
    parameter  type                   axi_req_t    = logic,
    parameter  type                   axi_resp_t   = logic,
    // Dependant parameters. DO NOT CHANGE!
    // Ara has NrLanes + 3 processing elements: each one of the lanes, the vector load unit, the
    // vector store unit, the slide unit, and the mask unit.
    localparam int           unsigned NrPEs        = NrLanes + 4,
    localparam type                   vlen_t       = logic[$clog2(VLEN+1)-1:0],
    localparam int           unsigned VLENB        = VLEN / 8
  ) (
    // Clock and Reset
    input  logic              clk_i,
    input  logic              rst_ni,
    // Scan chain
    input  logic              scan_enable_i,
    input  logic              scan_data_i,
    output logic              scan_data_o,

    // Interface with Ariane
    input  cva6_to_acc_t      acc_req_i,
    output acc_to_cva6_t      acc_resp_o,
    // AXI interface
    output axi_req_t          axi_req_o,
    input  axi_resp_t         axi_resp_i
  );

  `include "common_cells/registers.svh"
  `include "ara/ara_typedef.svh"
  import cf_math_pkg::idx_width;

  ///////////////////
  //  Definitions  //
  ///////////////////

  localparam int unsigned MaxVLenPerLane  = VLEN / NrLanes;       // In bits
  localparam int unsigned MaxVLenBPerLane = VLENB / NrLanes;      // In bytes
  localparam int unsigned VRFSizePerLane  = MaxVLenPerLane * 32;  // In bits
  localparam int unsigned VRFBSizePerLane = MaxVLenBPerLane * 32; // In bytes
  // Address of an element in each lane's VRF
  typedef logic [idx_width(VRFBSizePerLane)-1:0] vaddr_t;

  localparam int unsigned DataWidth = $bits(elen_t);
  localparam int unsigned StrbWidth = DataWidth / 8;
  typedef logic [StrbWidth-1:0] strb_t;
  localparam int unsigned AesColsPerLane = ELEN / 32;
  localparam int unsigned AesColsPerGroup = 4;

  if (Zvkned(CryptoSupport)) begin : gen_zvkned_cfg_checks
    initial begin
      if ((NrLanes * AesColsPerLane < AesColsPerGroup) ||
          (((NrLanes * AesColsPerLane) % AesColsPerGroup) != 0))
        $fatal(1,
               "Ara Zvkned requires NrLanes*(ELEN/32) to be a multiple of 4 and at least 4 AES columns per beat; got NrLanes=%0d, ELEN=%0d",
               NrLanes, ELEN);
      if (MaxVLenPerLane < ELEN)
        $fatal(1,
               "Ara Zvkned requires VLEN/NrLanes >= %0d bits so each lane can hold one 64-bit beat; got VLEN=%0d, NrLanes=%0d",
               ELEN, VLEN, NrLanes);
    end
  end

  // Interfaces between Ara's dispatcher and Ara's backend
  typedef struct packed {
    ara_op_e op; // Operation

    // Stores and slides do not re-shuffle the
    // source registers. In these two cases, vl refers
    // to the target EEW and vtype.vsew, respectively.
    // Since operand requesters work with the old
    // eew of the source registers, we should rescale
    // vl to the old eew to fetch the correct number of Bytes.
    //
    // Another solution would be to pass directly the target
    // eew (vstores) or the vtype.vsew (vslides), but this would
    // create confusion with the current naming convention
    logic scale_vl;

    // Mask vector register operand
    logic vm;
    rvv_pkg::vew_e eew_vmask;

    // 1st vector register operand
    logic [4:0] vs1;
    logic use_vs1;
    opqueue_conversion_e conversion_vs1;
    rvv_pkg::vew_e eew_vs1;
    rvv_pkg::vew_e old_eew_vs1;

    // 2nd vector register operand
    logic [4:0] vs2;
    logic use_vs2;
    opqueue_conversion_e conversion_vs2;
    rvv_pkg::vew_e eew_vs2;

    // Use vd as an operand as well (e.g., vmacc)
    logic use_vd_op;
    rvv_pkg::vew_e eew_vd_op;

    // Scalar operand
    elen_t scalar_op;
    logic use_scalar_op;

    // 2nd scalar operand: stride for constant-strided vector load/stores, slide offset for vector
    // slides
    elen_t stride;
    logic is_stride_np2;

    // Destination vector register
    logic [4:0] vd;
    logic use_vd;

    // If asserted: vs2 is kept in MulFPU opqueue C, and vd_op in MulFPU A
    logic swap_vs2_vd_op;

    // Effective length multiplier
    rvv_pkg::vlmul_e emul;

    // Number of segments in segment mem op
    logic [2:0] nf;

    // Is this a fault-only-first load?
    logic fault_only_first;

    // Rounding-Mode for FP operations
    fpnew_pkg::roundmode_e fp_rm;
    // Widen FP immediate (re-encoding)
    logic wide_fp_imm;
    // Resizing of FP conversions
    resize_e cvt_resize;

    // Vector machine metadata
    vlen_t vl;
    vlen_t vstart;
    rvv_pkg::vtype_t vtype;

    // Request token, for registration in the sequencer
    logic token;
  } ara_req_t;

  typedef struct packed {
    // Scalar response
    elen_t resp;

    // Instruction triggered an exception
    exception_t exception;

    // Fault-only-first exception on element whose idx > 0
    logic fof_exception;

    // New value for vstart
    vlen_t exception_vstart;
  } ara_resp_t;

  //////////////////
  //  Dispatcher  //
  //////////////////

  // Interface with the sequencer
  ara_req_t                     ara_req;
  logic                         ara_req_valid;
  logic                         ara_req_ready;
  ara_resp_t                    ara_resp;
  logic                         ara_resp_valid;
  logic                         ara_idle;
  // Interface with the VSTU
  logic                         core_st_pending;
  logic                         load_complete;
  logic                         store_complete;
  logic                         store_pending;
  // Interface with the lanes
  logic      [NrLanes-1:0][4:0] fflags_ex;
  logic      [NrLanes-1:0]      fflags_ex_valid;
  logic      [NrLanes-1:0]      vxsat_flag;
  vxrm_t     [NrLanes-1:0]      alu_vxrm;
  // Flush support for store exceptions
  logic lsu_ex_flush_lane, lsu_ex_flush_done;
  logic [NrLanes-1:0] lsu_ex_flush_stu;

  ara_dispatcher #(
    .CVA6Cfg           (CVA6Cfg           ),
    .NrLanes           (NrLanes           ),
    .VLEN              (VLEN              ),
    .FPUSupport        (FPUSupport        ),
    .SegSupport        (SegSupport        ),
    .CryptoSupport     (CryptoSupport     ),
    .ara_req_t         (ara_req_t         ),
    .ara_resp_t        (ara_resp_t        ),
    .accelerator_req_t (accelerator_req_t ),
    .accelerator_resp_t(accelerator_resp_t)
  ) i_dispatcher (
    .clk_i             (clk_i           ),
    .rst_ni            (rst_ni          ),
    // Interface with Ariane
    .acc_req_i         (acc_req_i.acc_req  ),
    .acc_resp_o        (acc_resp_o.acc_resp),
    // Interface with the sequencer
    .ara_req_o         (ara_req         ),
    .ara_req_valid_o   (ara_req_valid   ),
    .ara_req_ready_i   (ara_req_ready   ),
    .ara_resp_i        (ara_resp        ),
    .ara_resp_valid_i  (ara_resp_valid  ),
    .ara_idle_i        (ara_idle        ),
    // Interface with the lanes
    .vxsat_flag_i      (vxsat_flag      ),
    .alu_vxrm_o        (alu_vxrm        ),
    .fflags_ex_i       (fflags_ex       ),
    .fflags_ex_valid_i (fflags_ex_valid ),
    // Flush support
    .lsu_ex_flush_o     (lsu_ex_flush_lane),
    .lsu_ex_flush_done_i(lsu_ex_flush_done),
    // Interface with the Vector Store Unit
    .core_st_pending_o (core_st_pending ),
    .load_complete_i   (load_complete   ),
    .store_complete_i  (store_complete  ),
    .store_pending_i   (store_pending   )
  );

  /////////////////
  //  Sequencer  //
  /////////////////

  // Interface with the PEs
  pe_req_t                         pe_req;
  logic                            pe_req_valid;
  logic              [NrPEs-1:0]   pe_req_ready;
  logic              [NrVInsn-1:0] pe_vinsn_running;
  pe_resp_t          [NrPEs-1:0]   pe_resp;
  // Interface with the address generator
  logic                            addrgen_ack;
  exception_t                      addrgen_exception;
  vlen_t                           addrgen_exception_vstart;
  logic                            addrgen_fof_exception;
  logic                            lsu_current_burst_exception;
  logic              [NrLanes-1:0] alu_vinsn_done;
  logic              [NrLanes-1:0] mfpu_vinsn_done;
  // Interface with the operand requesters
  logic [NrVInsn-1:0][NrVInsn-1:0] global_hazard_table;
  // Ready for lane 0 (scalar operand fwd)
  logic pe_scalar_resp_ready;

  // Mask unit operands
  elen_t     [NrLanes-1:0][NrMaskFUnits+2-1:0] masku_operand;
  logic      [NrLanes-1:0][NrMaskFUnits+2-1:0] masku_operand_valid;
  logic      [NrLanes-1:0][NrMaskFUnits+2-1:0] masku_operand_ready_masku, masku_operand_ready_lane;
  strb_t     [NrLanes-1:0]                     mask;
  logic      [NrLanes-1:0]                     mask_valid;
  logic                                        mask_valid_lane;
  logic      [NrLanes-1:0]                     lane_mask_ready;

  // Mask unit scalar result variables
  elen_t     result_scalar;
  logic      result_scalar_valid;

  ara_sequencer #(
    .NrLanes      (NrLanes      ),
    .VLEN         (VLEN         ),
    .CryptoSupport(CryptoSupport),
    .ara_req_t    (ara_req_t    ),
    .ara_resp_t   (ara_resp_t   ),
    .pe_req_t     (pe_req_t     ),
    .pe_resp_t    (pe_resp_t    ),
    .exception_t  (exception_t  )
  ) i_sequencer (
    .clk_i                 (clk_i                    ),
    .rst_ni                (rst_ni                   ),
    // Interface with the dispatcher
    .ara_req_i             (ara_req                  ),
    .ara_req_valid_i       (ara_req_valid            ),
    .ara_req_ready_o       (ara_req_ready            ),
    .ara_resp_o            (ara_resp                 ),
    .ara_resp_valid_o      (ara_resp_valid           ),
    .ara_idle_o            (ara_idle                 ),
    // Interface with the PEs
    .pe_req_o              (pe_req                   ),
    .pe_req_valid_o        (pe_req_valid             ),
    .pe_vinsn_running_o    (pe_vinsn_running         ),
    .pe_req_ready_i        (pe_req_ready             ),
    .pe_resp_i             (pe_resp                  ),
    .alu_vinsn_done_i      (alu_vinsn_done[0]        ),
    .mfpu_vinsn_done_i     (mfpu_vinsn_done[0]       ),
    // Interface with the operand requesters
    .global_hazard_table_o (global_hazard_table      ),
    // Interface with the lane 0
    .pe_scalar_resp_i      (pe_req.op inside{[VCPOP:VFIRST]} ? result_scalar : masku_operand[0][1]), // MaskB OpQueue
    .pe_scalar_resp_valid_i(pe_req.op inside{[VCPOP:VFIRST]} ? result_scalar_valid : masku_operand_valid[0][1]), // MaskB OpQueue Valid
    .pe_scalar_resp_ready_o(pe_scalar_resp_ready     ),
    // Interface with the address generator
    .addrgen_ack_i         (addrgen_ack              ),
    .addrgen_exception_i   (addrgen_exception        ),
    .addrgen_exception_vstart_i(addrgen_exception_vstart),
    .addrgen_fof_exception_i(addrgen_fof_exception),
    .lsu_current_burst_exception_i(lsu_current_burst_exception)
  );

  // Scalar move support
  always_comb begin
    masku_operand_ready_lane = masku_operand_ready_masku;
    // The scalar move fetches the data from lane 0 - MaskB OpQueue (idx == 1)
    masku_operand_ready_lane[0][1] = masku_operand_ready_masku[0][1] | pe_scalar_resp_ready;
  end

  /////////////
  //  Lanes  //
  /////////////

  // Interface with the vector load/store unit
  // Store unit
  elen_t     [NrLanes-1:0]                     stu_operand;
  logic      [NrLanes-1:0]                     stu_operand_valid;
  logic      [NrLanes-1:0]                     stu_operand_ready;
  // Slide unit/address generation operands
  elen_t     [NrLanes-1:0]                     sldu_addrgen_operand;
  logic      [NrLanes-1:0]                     sldu_operand_valid;
  logic      [NrLanes-1:0]                     addrgen_operand_valid;
  logic      [NrLanes-1:0]                     sldu_operand_ready;
  sldu_mux_e                                   sldu_mux_sel;
  logic                                        addrgen_operand_ready;
  logic      [NrLanes-1:0]                     sldu_red_valid;

  // Results
  // Load Unit
  logic      [NrLanes-1:0]                     ldu_result_req;
  vid_t      [NrLanes-1:0]                     ldu_result_id;
  vaddr_t    [NrLanes-1:0]                     ldu_result_addr;
  elen_t     [NrLanes-1:0]                     ldu_result_wdata;
  strb_t     [NrLanes-1:0]                     ldu_result_be;
  logic      [NrLanes-1:0]                     ldu_result_gnt;
  logic      [NrLanes-1:0]                     ldu_result_final_gnt;
  // Slide Unit
  logic      [NrLanes-1:0]                     sldu_result_req;
  vid_t      [NrLanes-1:0]                     sldu_result_id;
  vaddr_t    [NrLanes-1:0]                     sldu_result_addr;
  elen_t     [NrLanes-1:0]                     sldu_result_wdata;
  strb_t     [NrLanes-1:0]                     sldu_result_be;
  logic      [NrLanes-1:0]                     sldu_result_gnt;
  logic      [NrLanes-1:0]                     sldu_result_final_gnt;
  // Mask Unit
  logic      [NrLanes-1:0]                     masku_result_req;
  vid_t      [NrLanes-1:0]                     masku_result_id;
  vaddr_t    [NrLanes-1:0]                     masku_result_addr;
  elen_t     [NrLanes-1:0]                     masku_result_wdata;
  strb_t     [NrLanes-1:0]                     masku_result_be;
  logic      [NrLanes-1:0]                     masku_result_gnt;
  logic      [NrLanes-1:0]                     masku_result_final_gnt;
  logic      [NrLanes-1:0]                     masku_vrgat_req_valid;
  logic      [NrLanes-1:0]                     masku_vrgat_req_ready;
  vrgat_req_t                                  masku_vrgat_req;

  // Cross-lane AES .vs key broadcast wiring.
  // For .vs instructions, the 128-bit round key lives in vs2[3:0], which maps
  // to lanes 0-3. Lanes 4+ need to receive the key from lane (l % 4).
  elen_t [NrLanes-1:0] aes_key_data;
  elen_t [NrLanes-1:0] aes_broadcast_key;
  if (Zvkned(CryptoSupport)) begin : gen_aes_broadcast
    for (genvar l = 0; l < NrLanes; l++) begin : gen_aes_broadcast
      assign aes_broadcast_key[l] = aes_key_data[l % 4];
    end
  end else begin : gen_no_aes_broadcast
    assign aes_broadcast_key = '0;
  end
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
