pulp-platform/ara/hardware/src/lane/vmfpu.sv

// Copyright 2021 ETH Zurich and University of Bologna.
// Solderpad Hardware License, Version 0.51, see LICENSE for details.
// SPDX-License-Identifier: SHL-0.51
//
// Authors: Matheus Cavalcante <matheusd@iis.ee.ethz.ch>
//          Matteo Perotti <mperotti@iis.ee.ethz.ch>
// Description:
// Ara's integer multiplier and floating-point unit.

module vmfpu import ara_pkg::*; import rvv_pkg::*; import fpnew_pkg::*;
  import cf_math_pkg::idx_width; #(
    parameter  int           unsigned NrLanes         = 0,
    parameter  int           unsigned VLEN            = 0,
    parameter  config_pkg::cva6_cfg_t CVA6Cfg         = cva6_config_pkg::cva6_cfg,
    // Support for floating-point data types
    parameter  fpu_support_e          FPUSupport      = FPUSupportHalfSingleDouble,
    // External support for vfrec7, vfrsqrt7, rounding-toward-odd
    parameter  fpext_support_e        FPExtSupport    = FPExtSupportEnable,
    // Support for fixed-point data types
    parameter  fixpt_support_e        FixPtSupport    = FixedPointEnable,
    // Type used to address vector register file elements
    parameter  type                   vaddr_t         = logic,
    parameter  type                   vfu_operation_t = logic,
    // Dependant parameters. DO NOT CHANGE!
    localparam int           unsigned DataWidth    = $bits(elen_t),
    localparam int           unsigned StrbWidth    = DataWidth/8,
    localparam type                   strb_t       = logic [DataWidth/8-1:0],
    localparam type                   vlen_t       = logic[$clog2(VLEN+1)-1:0]
  ) (
    input  logic                         clk_i,
    input  logic                         rst_ni,
    input  logic[idx_width(NrLanes)-1:0] lane_id_i,
    // Interface with Dispatcher
    output logic                         mfpu_vxsat_o,
    input  vxrm_t                        mfpu_vxrm_i,
    // Interface with CVA6
    output logic           [4:0]         fflags_ex_o,
    output logic                         fflags_ex_valid_o,
    // Interface with the lane sequencer
    input  vfu_operation_t               vfu_operation_i,
    input  logic                         vfu_operation_valid_i,
    output logic                         mfpu_ready_o,
    output logic           [NrVInsn-1:0] mfpu_vinsn_done_o,
    // Interface with the lane
    output logic                         fpu_red_complete_o,
    // Interface with the operand queues
    input  elen_t          [2:0]         mfpu_operand_i,
    input  logic           [2:0]         mfpu_operand_valid_i,
    output logic           [2:0]         mfpu_operand_ready_o,
    // Interface with the vector register file
    output logic                         mfpu_result_req_o,
    output vid_t                         mfpu_result_id_o,
    output vaddr_t                       mfpu_result_addr_o,
    output elen_t                        mfpu_result_wdata_o,
    output strb_t                        mfpu_result_be_o,
    input  logic                         mfpu_result_gnt_i,
    // Interface with the Slide Unit
    output logic                         mfpu_red_valid_o,
    input  logic                         mfpu_red_ready_i,
    input  elen_t                        sldu_operand_i,
    input  logic                         sldu_mfpu_valid_i,
    output logic                         sldu_mfpu_ready_o,
    // Interface with the Mask unit
    output elen_t                        mask_operand_o,
    output logic                         mask_operand_valid_o,
    input  logic                         mask_operand_ready_i,
    input  strb_t                        mask_i,
    input  logic                         mask_valid_i,
    output logic                         mask_ready_o
  );

  // Power gating registers
  `include "common_cells/registers.svh"

  ////////////////////////////////
  //  Vector instruction queue  //
  ////////////////////////////////

  // We store a certain number of in-flight vector instructions
  localparam VInsnQueueDepth = MfpuInsnQueueDepth;

  struct packed {
    vfu_operation_t [VInsnQueueDepth-1:0] vinsn;

    // Each instruction can be in one of the three execution phases.
    // - Being accepted (i.e., it is being stored for future execution in this
    //   vector functional unit).
    // - Being processed (i.e., its micro-operations are currently being processed
    //   by the corresponding functional units).
    // - Being issued (i.e., its micro-operations are currently being issued
    //   to the corresponding functional units).
    // - Being committed (i.e., its results are being written to the vector
    //   register file).
    // We need pointers to index which instruction is at each execution phase
    // between the VInsnQueueDepth instructions in memory.
    logic [idx_width(VInsnQueueDepth)-1:0] accept_pnt;
    logic [idx_width(VInsnQueueDepth)-1:0] issue_pnt;
    logic [idx_width(VInsnQueueDepth)-1:0] processing_pnt;
    logic [idx_width(VInsnQueueDepth)-1:0] commit_pnt;

    // We also need to count how many instructions are queueing to be
    // issued/committed, to avoid accepting more instructions than
    // we can handle.
    logic [idx_width(VInsnQueueDepth):0] issue_cnt;
    logic [idx_width(VInsnQueueDepth):0] processing_cnt;
    logic [idx_width(VInsnQueueDepth):0] commit_cnt;
  } vinsn_queue_d, vinsn_queue_q;

  // Is the vector instruction queue full?
  logic vinsn_queue_full;
  assign vinsn_queue_full = (vinsn_queue_q.commit_cnt == VInsnQueueDepth);
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
